krampslaag/Bikera/Componenten.docx

PCB componenten

# 1 Overzicht

- MCU: STM32, energiezuinig
- Lora transceiver
- EEC chip: elliptische curve berekening
- GPS/GNSS module
- E-ink display
- Accelerometer
- SD-kaart
- BMS voor 2-4 18650 batterijen
- Aansturing voor motor of solenoide

# 2 MCU: STM32

- Energiezuinig
- Net genoeg rekenkracht
- Geen zware crypto (externe EEC chip)

## 2.1 Flash schatting

Component | Flash
Boot + main app | ~10–20 kB
LoRaWAN stack | 20–40 kB
Drivers (SPI, I²C, UART) | 5–10 kB
QR-code lib | 5–10 kB
Display driver | 5–15 kB
Debug / utils | 5–10 kB

Minimim flash:

64 kB = krap
128 kB = comfortabel
256 kB = luxe

## 2.2 RAM schatting

Component | RAM
Stack + heap | ~4 kB
LoRa buffers | 2–4 kB
QR matrix | 1–2 kB
Display buffer (partial) | 1–4 kB
Sensor buffers | <1 kB

Minimum RAM:

16 kB = minimum
32 kB = veilig
64 kB = chill debuggen

## 2.3 Peripherals

Het is nog niet duidelijk welke modules met SPI, I²C of UART werken

Peripheral | | Aantal pinnen
SPI | - Lora transceiver - e-ink - SD-kaart | 3 (clk, miso, mosi) + 3 (cs)
I²C | - accelerometer | 2
UART | - GPS/GNSS - Bluetooth - debug logs | 2 2 2
ADC 10-12 bit | - Batterij spanning | 1
Timers (Intern) | - RTC wakeups - debouncing knoppen - watchdog
GPIO | Interrupts: - knoppen - Lora DIO - accelerometer - Motor/solenoid - Status LED | 2-4 1-3 ? 1 1-2 1
SWD | Serial wire debug | 2
NRST pin | Reset pin | 1
| | +2 (VCC en GND) = 24-31 totaal

## 2.4 Vereisten

- Cortex-M0+ of hoger
- ≥ 128 kB Flash
- ≥ 32 kB RAM
- 3× SPI (met DMA)
- 2× UART
- I²C
- ADC
- RTC
- Ultra-low power sleep modes
- SWD debug

Aantal SPI, UART en I²C is een gok, de meeste chips hebben wel genoeg van elk

## 2.5 Opties

https://www.rutronik.com/fileadmin/Rutronik/Supplier/STMicroelectronics/Landing_Pages/STM32L496xx_Family/RS4386_brstm32ulp.pdf

STM32L0 (https://www.st.com/en/microcontrollers-microprocessors/stm32l0-series.html) Cortex-M0+ Goedkoopste, meest zuinig, misschien net niet genoeg flash en RAM

STM32L1 (https://www.st.com/en/microcontrollers-microprocessors/stm32l1-series.html) Cortex-M3+ Iets krachtiger, iets minder zuinig

STM32L4 (https://www.st.com/en/microcontrollers-microprocessors/stm32l4-series.html) Cortex-M4 Nog krachtiger, ongeveer even zuinig als L0, duurder

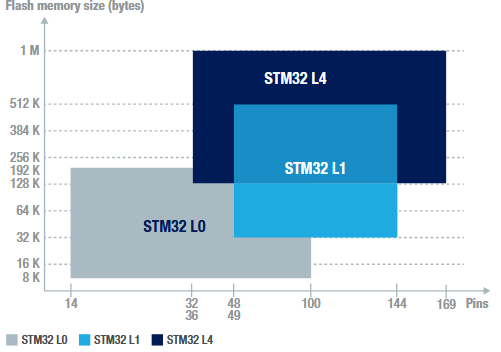
[picture p2: figure]
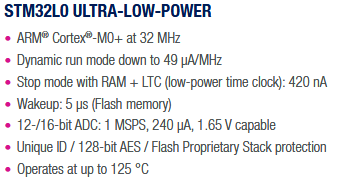
[picture p3: figure]
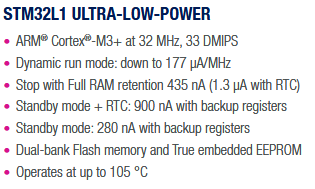
[picture p4: figure]
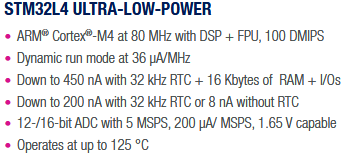
[picture p5: figure]
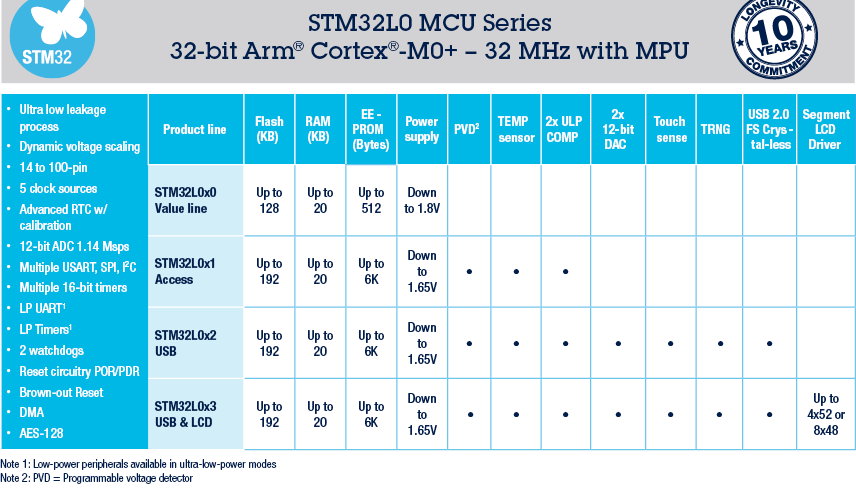
[picture p6: figure]
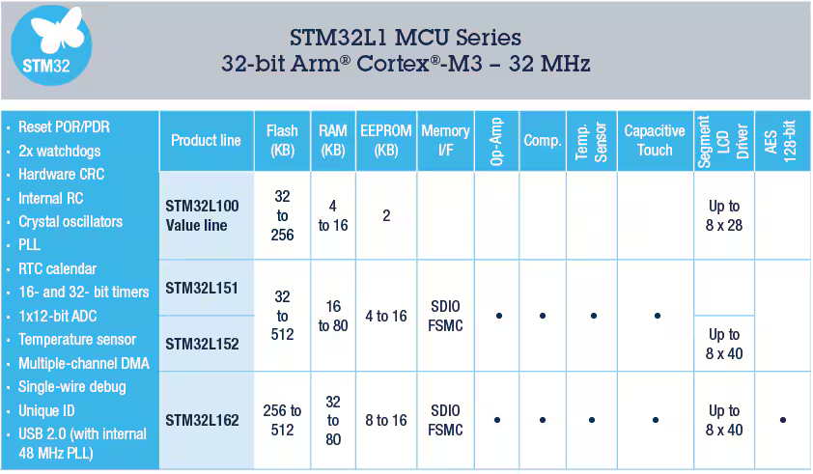
[picture p7: figure]
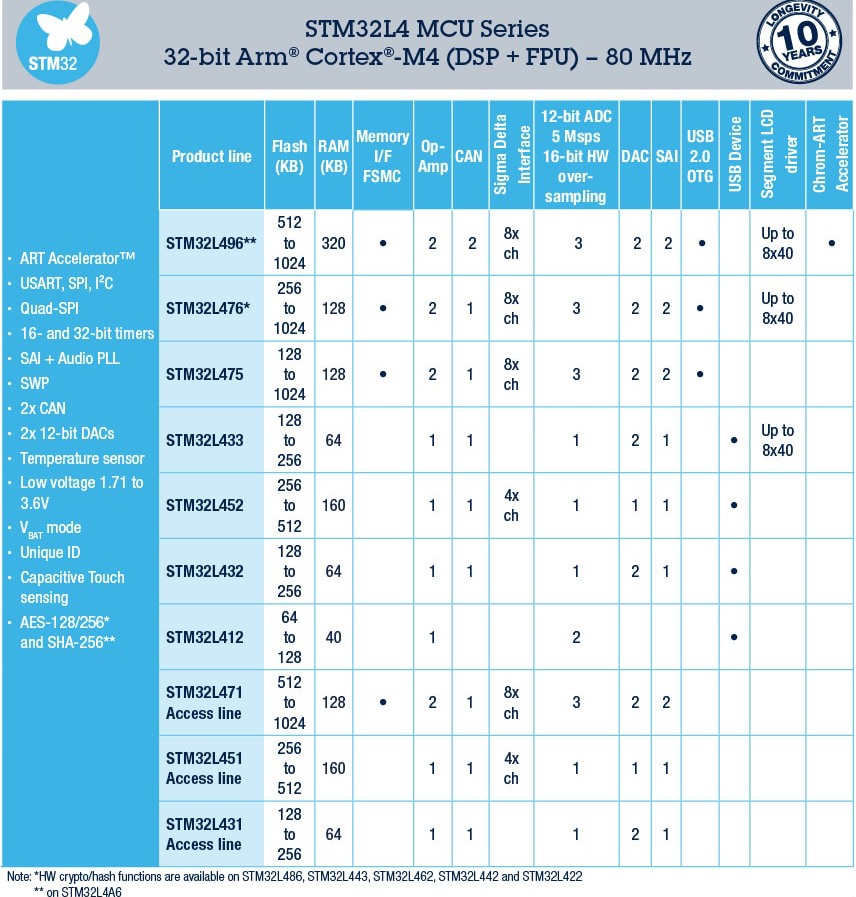
[picture p8: figure]
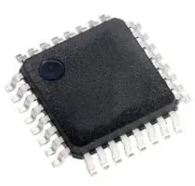
[picture p9: figure]

## 2.6 Vormfactor

24-31 pinnen nodig

Bij voorkeur LQFP32 of LQFP48

## 2.7 Voorbeeld van prijzen

https://www.digikey.be/en/products/filter/embedded-microcontrollers/685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

https://be.farnell.com/w/c/semiconductors-ics/microcontrollers/arm-microcontrollers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

## 2.8 Voorstel

Flash RAM pinnen

STM32L431CCT6TR (https://be.farnell.com/stmicroelectronics/stm32l431cct6tr/mcu-32bit-80mhz-lqfp-48/dp/3365485RL) Cortex-M4 256KB 64KB 48

STM32L071CZT6TR (https://be.farnell.com/stmicroelectronics/stm32l071czt6tr/mcu-32bit-32mhz-lqfp-48/dp/3365483RL) Cortex-M0+ 192KB 20KB 48

STM32L412CBT6P (https://be.farnell.com/stmicroelectronics/stm32l412cbt6p/mcu-32bit-80mhz-lqfp-48/dp/3933166) Cortex-M4 128KB 40KB 48

STM32L412KBT6 (https://be.farnell.com/stmicroelectronics/stm32l412kbt6/mcu-32bit-80mhz-lqfp-32/dp/2980922) Cortex-M4 128KB 40KB 32

STM32L422KBT6 (https://be.farnell.com/stmicroelectronics/stm32l422kbt6/mcu-32bit-80mhz-lqfp-32/dp/2980927) Cortex-M4 128KB 40KB 32

Zie vergelijking volgende pagina (Farnell)

Digikey lijkt goedkoper bij grote hoeveelheden (rangschik per prijs en kies price by quantity)

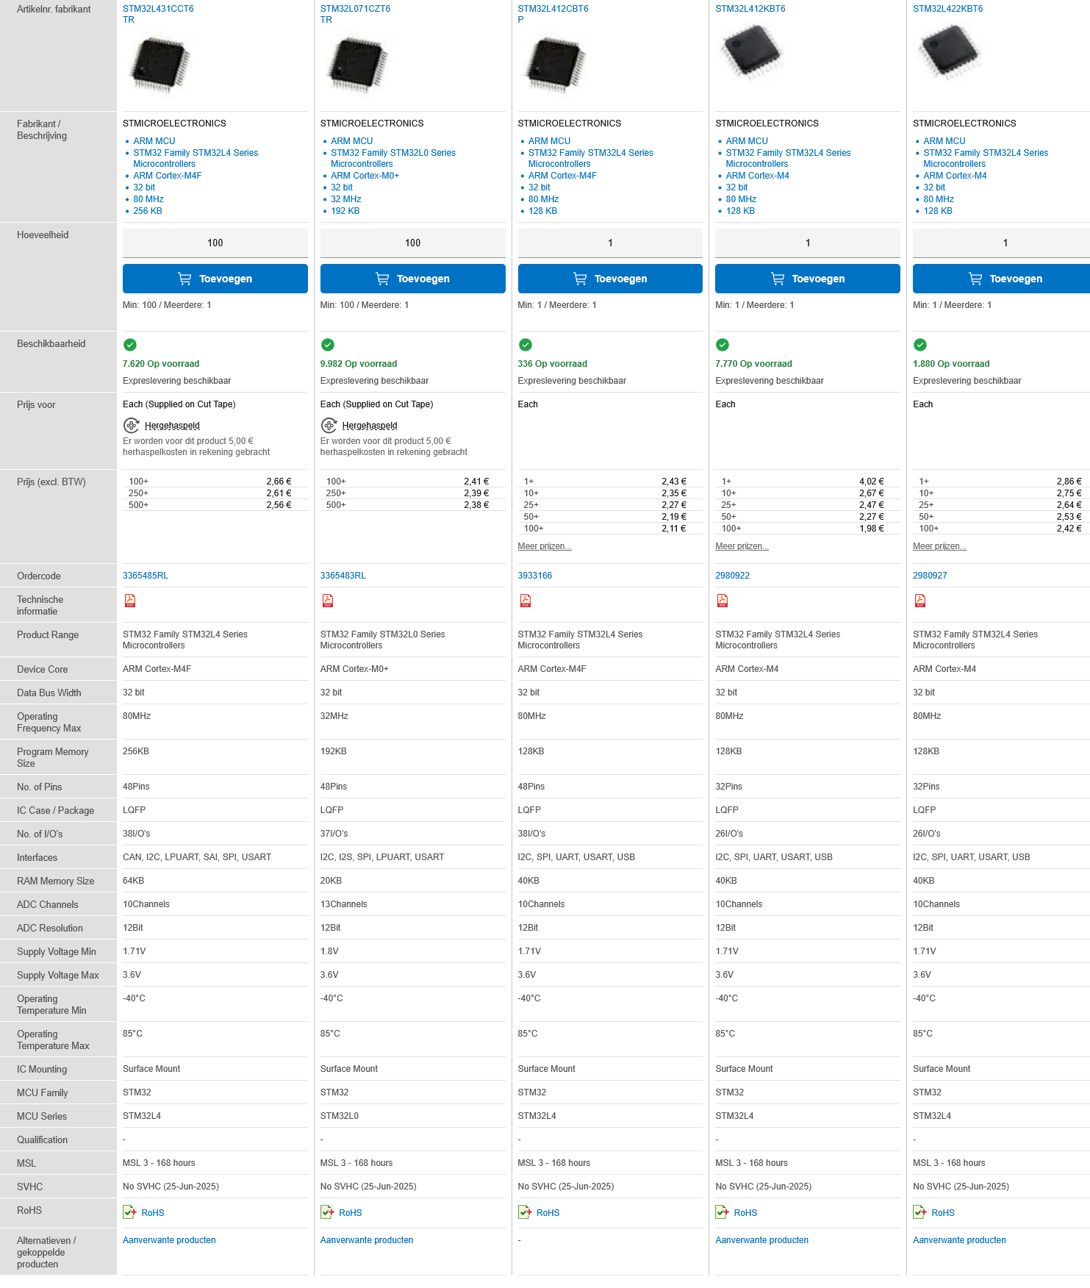
[picture p10: figure]

## 2.9 Keuze

Voor prototype:

STM32L431CCT6TR (https://be.farnell.com/stmicroelectronics/stm32l431cct6tr/mcu-32bit-80mhz-lqfp-48/dp/3365485RL) Cortex-M4 256KB flash 64KB ram LQFP-48

# 3 LoRa

- 868MHz voor Europa (863–870 MHz / EU868 / ISM band)
- LoRaWAN
- CE-gecertificeerd
- ETSI EN 300 220-conform
- RX-stroom ≈ 4–6 mA ?
- TX-stroom ≈ 40–120 mA (afhankelijk van het vermogen) ?
- Slaapstroom < 2 µA (idealiter < 1 µA)?
- SPI: betere timing, efficienter dan UART

Opties:

- Transceiver IC
  - bv. SX1261, SX1262, LLCC68 (SX127x is verouderd en minder efficient)
  - RF matching en antenne design zelf doen
- LoRa module
  - RF is al gedaan, gecertificeerd, alleen SPI + antenne
- STM32WL SoCs = STM32 + LoRa
  - Efficienter, goedkoper, moeilijker mee te werken

## 3.1 STM32 + LoRa?

STM32WL serie bevat LoRa radio

https://www.st.com/en/microcontrollers-microprocessors/stm32wl5x-ex.html

- Efficienter (geen SPI/UART, geen externe radio wakeups)
- I-CUBE-LRWAN en LoRaWAN stacks aangeboden door ST
- Goedkoper dan lora apart
- RF ontwerp moeilijker (antenne interface, ground keep-outs)
- Moeilijkere configuratie (EU regels, RF matching zelf instellen,…)
- Moeilijkere vormfactor (UQFPN, UFBGA)

## 3.2 Modules

Ebyte E22 series (https://www.cdebyte.com/Module-LoRa-SX1262)

- Bv. E22-900M30S, E22-900M22S, E22P-868M30S
- Gebaseerd op SX1262
- SPI
- Chinees, niet op digikey, farnell, mouser

WisDuo RAK3172 (https://docs.rakwireless.com/product-categories/wisduo/rak3172-module/overview/)

- met STM32WLE5CCU6
- UART interface
- SPI mogelijk?? “SPI voor communicatie met RF subsysteem van STM32WLE5CCU6”
- https://www.digikey.be/nl/products/detail/rakwireless-technology-limited/RAK3172-8-SM-NI/17138049

WisDuo RAK11720 (https://store.rakwireless.com/products/rak11720-ambiq-apollo3-module-for-lorawan?variant=43549376250054)

- LoRa + BLE 5
- https://www.digikey.be/nl/products/filter/rf-misc-ic-s-en-modules/863?s=N4IgTCBcDaIEoEEDSBGFB2MAGEBdAvkA

Murata CMWX1ZZABZ

- Zeer compact, duurder

Eventueel met GPS/GNSS:

LoRa Edge (https://wyldnetworks.com/blog/semtech-lora-edge-for-asset-tracking)

https://www.mouser.be/ProductDetail/Semtech/LR1110IMLTRT?qs=GedFDFLaBXFCcMA0cJwOqg%3D%3D

## 3.3 Keuze

Voor prototype:

WisDuo RAK11720 (https://store.rakwireless.com/products/rak11720-ambiq-apollo3-module-for-lorawan?variant=43549376250054)

Met MHF4 connector: https://www.digikey.be/nl/products/detail/rakwireless-technology-limited/RAK11720-8-SM-I/26861631

RF pinout: https://www.digikey.be/nl/products/detail/rakwireless-technology-limited/RAK11720-8-SM-NI/26861635

## 3.4 Antenne

WisDuo RAK11720 (https://store.rakwireless.com/products/rak11720-ambiq-apollo3-module-for-lorawan?variant=43549376250054) heeft 2 connectors, voor LoRa en BLE

### 3.4.1 RAK11720 LoRa vereisten

- 868MHz
- MHF4 connector
- 50Ω impedantie
- VSWR <= 2 of return loss < -10dB (beter VSWR <= 1.5 of return loss < -15dB)
- Gain 0–3 dBi (hoger wordt directioneel, verder bereik op vlak terrein maar minder geschikt voor steden)
- Lengte: ½ of ¼ golflengte (868MHz) is geschikt: ~8.6cm tot 17.3cm

### 3.4.2 Soorten antennes

- Antenne op PCB :
  - Goedkoper in productie
  - Moeilijker, gevoelig voor layout en enclosure, RF ervaring nodig
- FPC antenne: Met een draad naar flex PCB om te plakken
  - Eenvoudig, vrij compact
  - Gemakkelijkere certificatie
- Coil antenne: niet geschikt voor vibratie en schokken
- Externe antenne: niet geschikt voor fietsslot

FPC antenne voor prototype, eventueel PCB antenne later?

### 3.4.3 Opties

Op digikey zijn er 2 met MHF4 aansluiting en 868MHz.

3dB versterking, VSWR 2.5, €1 voor 1

https://www.digikey.be/nl/products/filter/rf-antennes/875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

Beste resultaat op farnell:

2.2dBi, VSWR 1.5, €2.69 voor 1

https://be.farnell.com/te-connectivity/l000551-05/rf-antenna-863-to-870mhz-2-2dbi/dp/4457734

### 3.4.4 Keuze

Voor prototype: farnell

Later losse draad? Zal moeten getest worden.

### 3.4.5 Losse draad

½ of ¼ golflengte: 8.6 cm of 17.2 cm

Impedantie moet ~50 Ω zijn voor RAK11720

Moeilijk te testen op MHF4-connector voor prototype, eventueel RF pinout gebruiken later?

Monopool

1 draad gebogen rond binnenkant van behuizing

Goede groundplane nodig

Beter met RF pinout (niet MHF4)

Ideale impedantie en VSWR bij resonantie (perfecte geometrie, rechte antenne):

8.6 cm: ~ 73 Ω , VSWR ≈ 1.5

17.2 cm: ~36-39 Ω, VSWR ≈ 1.3 – 1.6

8.6cm monopool in fietsslot:

  - Resonantiefrequentie kan zakken (en VSWR stijgen)
  - Impedantie kan 20-60Ω zijn met wat reactantie
  - VSWR kan 1.2-3 zijn afhankelijk van de layout

17.2 cm monopool in fietsslot:

  - Veel reactantie, hoge VSWR
  - Wordt niet veel gebruikt

Dipool

- 2x 8.6 cm
- Gebogen, of licht gebogen in V-vorm of evt. recht in V-vorm
- In vrije ruimte, recht:
  - Impedantie ≈ 73 Ω bij resonantie
  - VSWR op 50 Ω ≈ 1.5:1
- Gebogen in fietsslot:
  - Resonantie zal zakken
  - Impedantie kan dichter bij 50 Ω zakken
  - Draad inkorten kan resonantie terug naar 868MHz brengen
  - Positie (horizontaal, verticaal) bepaalt uitstraling

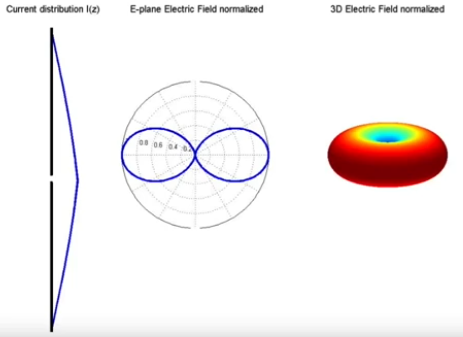
[picture p11: figure]

Suggestie: dipool in V-vorm, recht of licht gebogen. Beginnen met 2x9cm en trimmen tot resonantie 868MHz is, impedantie ongeveer 50 Ω en VSWR laag genoeg. Of tot prestatie goed is.

### 3.4.6 BLE

Aparte antenne nodig voor BLE (WisDuo RAK11720 (https://store.rakwireless.com/products/rak11720-ambiq-apollo3-module-for-lorawan?variant=43549376250054) heeft 2 connectors)

Vereisten:

- 2.4-2.5GHz, 50Ω MHF4 bluetooth antenne.
- Gain: 0-3dBi (=omnidirectioneel) & goede uitstralingsefficientie (>=40-50%)
- VSWR < 2:1 (≈ −10 dB return loss)
- Lange kabels kunnen ruis opnemen, kort is beter
- Best omnidirectioneel, orientatie maakt niet veel uit.

Soorten antennes: zoals LoRa. FPC antenne lijkt best.

Opties:

- Digikey (https://www.digikey.be/nl/products/filter/rf-antennes/875):

AANI-FB-0086-0100W lijkt best, is beschikbaar in 3 lengtes: 100mm (https://www.digikey.be/nl/products/detail/abracon-llc/AANI-FB-0086-0100W/25558929), 150mm (https://www.digikey.be/nl/products/detail/abracon-llc/AANI-FB-0086-0150W/25558928), 200mm (https://www.digikey.be/nl/products/detail/abracon-llc/AANI-FB-0086-0200W/25558936)

€2.14 - €2.21

- De site van de RAK module raadt deze aan ($3): https://store.rakwireless.com/products/2-4ghz-wifi-ble-pcb-antenna-mhf-4
- Bij Farnell zijn er geen FPC-antennes van 2.4GHz
- Bij Mouser zijn er maar 2 geschikte (https://www.mouser.be/c/passive-components/antennas/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) bluetooth antennes met MFH4 aansluiting, van €4.35 en €4.84

Keuze:

AANI-FB-0086-0100W (100mm) (https://www.digikey.be/nl/products/detail/abracon-llc/AANI-FB-0086-0100W/25558929) - €2.21 voor 1

# 4 ECC secure element

## 4.1 Vereisten

- Low power (slaapstroom < 1µA)
- I²C
- NVM key storage, root of trust ·
- Niet NIST P-256
  - Solana: Ed25519
  - Of Ethereum: Keccak-256
- SHA-256 (hash) voor transacties
- DIP vormfactor of DIP breakout voor socket (bv. SOIC-to-DIP)

## 4.2 Opties:

### 4.2.1 Microchip CryptoAuthentication serie

Microchip ATECC108A (https://ww1.microchip.com/downloads/aemDocuments/documents/OTH/ProductDocuments/DataSheets/Atmel-8895S-CryptoAuth-ATECC108A-Datasheet-Summary.pdf): voor key storage en ECDSA (Elliptic Curve Digital Signature Algorithm)

Microchip ATECC508A (https://ww1.microchip.com/downloads/en/DeviceDoc/20005928A.pdf): heeft ook ECDH (Elliptic Curve Diffie-Hellman) en secure boot

Microchip ATECC608A (https://www.mouser.com/datasheet/2/268/ATECC608A_CryptoAuthentication_Device_Summary_Data-3441583.pdf) / ATECC608B (https://ww1.microchip.com/downloads/aemDocuments/documents/SCBU/ProductDocuments/DataSheets/ATECC608B-CryptoAuthentication-Device-Summary-Data-Sheet-DS4000223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): meer geavanceerd (TLS 1.3, AES, betere security)

- TECC608B is hetzelfde als ATECC608A, met een paar kleine verbeteringen. ATECC608A heeft I²C problemen. https://ww1.microchip.com/downloads/en/Appnotes/Migrating-from-the-ATECC608A-to-the-ATECC608B-DS40002237A.pdf
- Slaapstroom <150 nA, actief 2–3 mA
- NIST P‑256
- ECDSA/ECDH met secure key storage
- AES-128: Encrypt/Decrypt
- I²C en single wire
- 8-pin SOIC en UDFN

### 4.2.2 ATECC608B device ordering codes

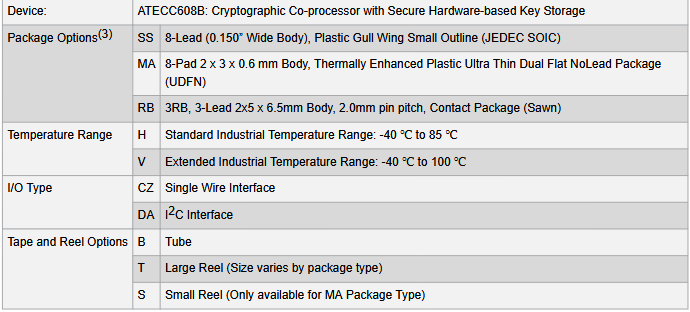
[picture p12: figure]

### 4.2.3 NXP EdgeLock SE050 (https://www.mouser.be/new/nxp-semiconductors/nxp-edgelock-se050/)

- Higher-end, meer features (CC EAL 6+ / FIPS-class security, TLS offload, meer algoritmes)
- Duurder
- HX2QFN20 vormfactor, voor reflow solderen

## 4.3 Keuze

Prototype: ATECC608B-SSHDA-T

8-pin SOIC, I²C, tape & reel

Digikey (https://www.digikey.be/nl/products/detail/microchip-technology/ATECC608B-SSHDA-T/13415162): €0.76 (€0.7488 voor 25 en €0.68541 voor 4000)

Mouser (https://www.mouser.be/ProductDetail/Microchip-Technology/ATECC608B-SSHDA-T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): €0.77 (0.649 voor >25)

Farnell (https://be.farnell.com/microchip/atecc608a-sshda-t/cryptoauthentication-40-to-85deg/dp/2920872):

Eventueel NXP EdgeLock SE050 (https://www.mouser.be/new/nxp-semiconductors/nxp-edgelock-se050/)

## 4.4 SOIC-to-DIP adapter

De ECC-chip wordt op een IC-voet geplaatst. De ATECC608B-SSHDA-T is een SMD component (SOIC-8) en heeft een SOIC-8-to-DIP adapter nodig.

- FIT0290 (https://www.digikey.nl/en/products/detail/dfrobot/FIT0290/6588424)
  - €0.47 digikey, inclusief pin headers

## 4.5 IC-voet

- 1-2199298-2 (https://www.te.com/commerce/DocumentDelivery/DDEController?Action=srchrtrv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)
  - €0.206 mouser (https://www.mouser.be/ProductDetail/TE-Connectivity/1-2199298-2?qs=fK8dlpkaUMtEKa4wabwOXQ%3D%3D)

# 5 GPS/GNSS

GPS zal alleen gebruikt worden als de fiets gestolen is. Locatiebepaling en snelheid/afstand meten gebeurt met de accelerometer en LoRa.

## 5.1 Vereisten

- Multi‑GNSS (GPS + Galileo + BeiDou + GLONASS) is meer precies en betrouwbaar, maar ook duurder
- Low power (sub‑mW standby)
- Meter-level precisie is genoeg
- Update rate (communicatie met MCU) en fix rate (Locatiebepaling) mogen laag zijn -> 1Hz, of zelfs kleiner?
- Interface: UART of I2C
- Geschikt voor buiten

## 5.2 Opties

U-blox en Quectel hebben goede modules

### 5.2.1 U-blox

MAX-M10 series (https://www.u-blox.com/en/product/max-m10-series)

- Ultra low power (<25mW)
- GPS, GLONASS, Galileo, BeiDou
- Goede performance met kleine antennes
- MAX-M10M-20B is nieuw en heeft ook:
  - SBAS (Satellite-Based Augmentation System)
  - LNA (low noise amplifier)
  - SAW filter (Surface Acoustic Wave)
- Goedkoopste modules op mouser (https://www.mouser.be/c/embedded-solutions/wireless-rf-modules/gnss-gps-modules/?q=u-blox&sort=pricing)

MAX-M10M-20B (https://www.mouser.be/datasheet/3/3699/1/MAX_M10M_20B_DataSheet_UBXDOC_963802114_13063.pdf) lijkt de beste optie van U-blox

- Mouser (https://www.mouser.be/ProductDetail/u-blox/MAX-M10M-20B?qs=bpu3f%2FCR1jxLHPI3qGoNEA%3D%3D): €5.53, Nieuw: beschikbaar vanaf 09/04/26
- Digikey (https://www.digikey.be/nl/products/detail/u-blox/MAX-M10M-20B/28314774?s=N4IgTCBcDaILIEEAaBaOBGADHFZMCEQBdAXyA): €5.84 (€5.2 per 1000)
- Niet bij Farnell
- Verbruik, ter vergelijking met Quectel:

### 5.2.2 Quectel

Zie brochure (https://www.quectel.com/content/uploads/2026/01/Quectel_Product_Brochure_V8.5_2026.pdf) p.91-93 (88-90 op blad) voor vergelijking

Goedkoopste modules op Digikey (https://www.digikey.be/nl/products/filter/rf-zendontvangermodules-en-modems/872)

Goedkoopste modules op Mouser

(https://www.mouser.be/c/rf-wireless/wireless-modules/gnss-gps-modules/?m=Quectel&sort=pricing)

LC76G serie

- (https://www.quectel.com/content/uploads/2024/03/Quectel_LC76G_Series_GNSS_Specification_V1.1-1-1.pdf)Goedkoop
- GPS, GLONASS, BDS, Galileo and QZSS
- AGNSS: snellere opstart (first time to fix) -> niet relevant (sattelietdata moet gedownload worden)
- Integrated LNA
- LC76G (PA) heeft laagste verbruik (10mA operatie, 5.5mA ALP mode, 13µA backup mode)
- Mouser prijzen: LC76GABMD (https://www.mouser.be/ProductDetail/Quectel/LC76GABMD?qs=vvQtp7zwQdPmNdoEwjtHVg%3D%3D) LC76GPAMD (https://www.mouser.be/ProductDetail/Quectel/LC76GPAMD?qs=vvQtp7zwQdMfDuCTmjRUww%3D%3D) LC76GPBMD (https://www.mouser.be/ProductDetail/Quectel/LC76GPBMD?qs=17ckDYBRdelT6eALYgwPNA%3D%3D)

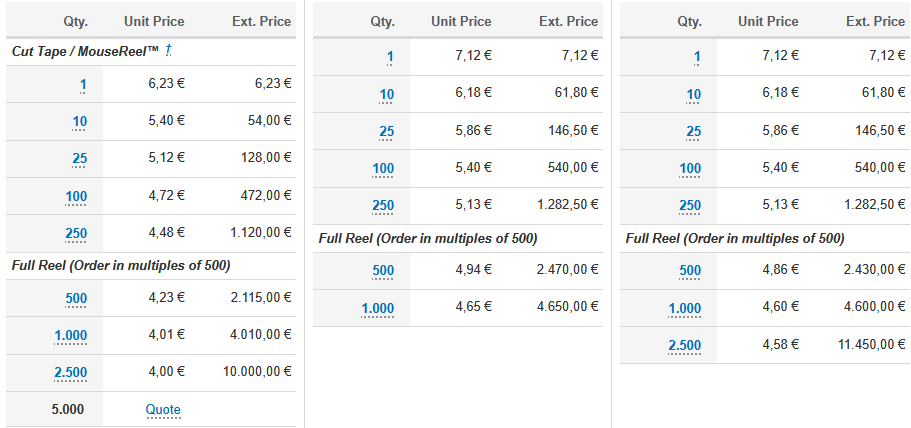
[picture p13: figure]

- Digikey prijzen:

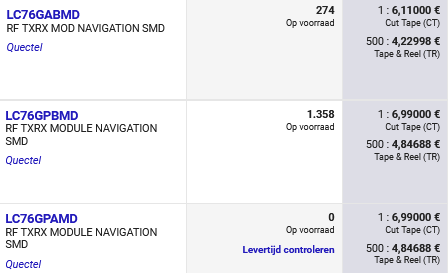
[picture p14: figure]

Quectel LC760Z (https://www.quectel.com/content/uploads/2025/03/Quectel_LC760Z_GNSS_Specification_V1.3.pdf)

- Goedkoopste Mouser (https://www.mouser.be/ProductDetail/Quectel/LC760Z00AAMD) Digikey (https://www.digikey.be/nl/products/detail/quectel/LC760Z00AAMD/22214009?s=N4IgTCBcDaIDIGEDsA2ADALRAXQL5A) (niet in voorraad)

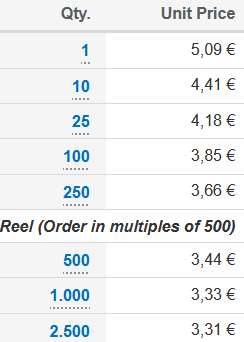
[picture p15: figure]
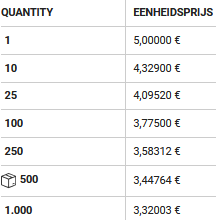
[picture p16: figure]

- GPS, GLONASS, Galileo, BDS (B1I & B1C) and QZSS
- Iets meer verbruik in operatie, standby mode van 1.4mA

Ter vergelijking: verbruik van U-blox MAX-M10M-20B (https://www.mouser.be/datasheet/3/3699/1/MAX_M10M_20B_DataSheet_UBXDOC_963802114_13063.pdf):

## 5.3 Voorstel:

U-blox MAX-M10M-20B (https://www.mouser.be/datasheet/3/3699/1/MAX_M10M_20B_DataSheet_UBXDOC_963802114_13063.pdf)

Of Quectel LC76GPAMD (https://www.mouser.be/ProductDetail/Quectel/LC76GPAMD?qs=vvQtp7zwQdMfDuCTmjRUww%3D%3D)

Quectel LC76GPAMD (https://www.mouser.be/ProductDetail/Quectel/LC76GPAMD?qs=vvQtp7zwQdMfDuCTmjRUww%3D%3D) heeft minder stroomverbruik en is goedkoper bij grote volumes.

U-blox MAX-M10M-20B (https://www.mouser.be/datasheet/3/3699/1/MAX_M10M_20B_DataSheet_UBXDOC_963802114_13063.pdf) heeft beter ecosysteem (u-center, AssistNow, veel voorbeeldontwerpen) en is beter voor kleine/slechte antennes, (SAW+LNA & Super-S technologie). Stroomverbruik is ook al klein.

## 5.4 Keuze

Quectel LC76GPAMD (https://www.mouser.be/ProductDetail/Quectel/LC76GPAMD?qs=vvQtp7zwQdMfDuCTmjRUww%3D%3D)

# 6 GPS antenne

Er zijn actieve en passieve GPS antennes. Actieve antennes zijn nauwkeuriger, hebben een geïntegreerde LNA (low noise amplifier) en hebben voeding nodig. Ze zijn beter geschikt om verder van de ontvanger te plaatsen. Passieve antennes zijn eenvoudiger, goedkoper, zuiniger en nauwkeurig genoeg voor deze toepassing. De Quectel LC76GPAMD (https://www.mouser.be/ProductDetail/Quectel/LC76GPAMD?qs=vvQtp7zwQdMfDuCTmjRUww%3D%3D) heeft ook een ingebouwde LNA.

## 6.1 Opties

## 6.2 Soorten antennes

- Helical antenna
- patch antenne

## 6.3 Vereisten

- 1-10m nauwkeurigheid is genoeg
- De datasheet (https://www.sigmaelectronica.net/wp-content/uploads/2024/07/quectel_lc76g_series_hardware_design_v1-2.pdf) (p. 38) toont deze specificaties voor een passieve antenne:

Frequency Range: 1559–1606 MHz

Polarization: RHCP (right-hand circular polarization)

VSWR: < 2 (Typ.)

Passive Antenna Gain: > 0 dBi

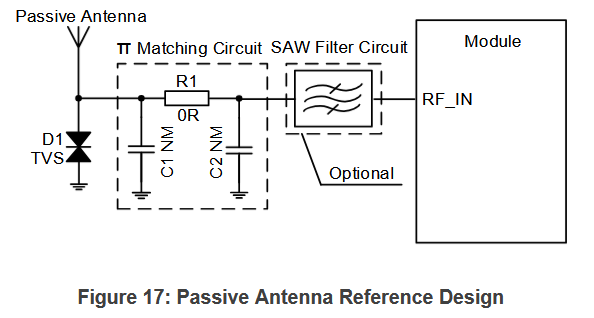
[picture p17: figure]

C1, R1, and C2 are reserved for matching antenna impedance. By default, R1 is 0 Ω, and C1 and C2 are

not mounted. They should be placed near the antenna in the actual layout. D1 is an electrostatic

discharge (ESD) protection device to protect the RF signal input from the potential damage caused by

ESD. The junction capacitance of D1 cannot be more than 0.6 pF and a transient voltage suppressor is

recommended. RF trace impedance should be controlled to 50 Ω and trace length should be kept as

short as possible.

## 6.4 Keuze

Voor prototype: YFGA003AA (https://www.digikey.be/nl/products/detail/quectel/YFGA003AA/21273116) FPC antenne

- €1.31
- 100mm kabel
- Er is een aparte connector nodig, de Quectel LC76GPAMD (https://www.mouser.be/ProductDetail/Quectel/LC76GPAMD?qs=vvQtp7zwQdMfDuCTmjRUww%3D%3D) GPS heeft geen connector.
- Eventueel kunnen we de kabel proberen doorknippen en rechtstreeks solderen

Later kunnen we een patch antenne proberen, of een draadantenne zoals bij LoRa.

# 7 E-ink display

## 7.1 Vereisten

- Zwart-wit, hoog contrast
- Grootte en resolutie
  - Klein, vierkant
  - 1.54 inch
  - Voldoende pixels voor QR
  - 1.54″ 200×200 wordt veel gebruikt voor QR codes
- QR code versie? (zie https://www.qrcode.com/en/about/version.html)
  - 21x21 is kleinst
  - Berekening grootst mogelijke QR code: De kleinste scanbare QR code is 1x1cm 38x38 pixel -> 0.263mm per pixel 1.54” = 27.12x27.12mm -> 200x200 pixels = 0.135mm per pixel kleinste mogelijke QR pixel is 2x2 pixels op het scherm (0.27x0.27mm) dus grootste QR code is 97x97 (versie 20)
- I²C of SPI?
  - I2C is efficienter op lage snelheden
  - De meeste E-inks zijn SPI
  - Scherm wordt niet veel ge-update, SPI is ok
- geen partial refresh of fast update nodig

## 7.2 Paneel of module?

### 7.2.1 Paneel

- SPI via korte flat-flex (FPC) kabel ( 0.5mm pitch, 22 of 24Pin)
  - Kan verlengd worden
- Fragiel
- Goedkoper
- Analoge front-end zelf ontwerpen (voedingscircuit: VGH, VGL, AVDD/VSH, VCOM,…)
  - Circuit hangt af van paneel, moet veranderd worden als paneel wordt veranderd
- Monteren op aparte PCB
- Specifieke driver per paneel

### 7.2.2 Module

- Veel eenvoudiger voor prototype
- Later kan schema van datasheet gekopieerd worden naar PCB en paneel gebruikt worden.

### 7.2.3 Andere opties

- Paneel + adapter board (https://eckstein-shop.de/GooDisplay-24Pin-Serial-ePaper-Screen-HAT-Adapter-Board-DESPI-C02-EN): met voedingscircuit
- Een driver board met ESP32 of ESP8266 bestaat ook, maar is meer bedoeld voor wifi

### 7.2.4 Opties

Panelen:

- Orient Display 1.54” 200x200 paneel (https://www.digikey.be/nl/products/detail/orient-display/AES200200A00-1-54ENRS/15198467)
  - Enige bij digikey
  - $7.2, niet beschikbaar in €
- Geen 1.54” E-inks bij Mouser of Farnell
- Good Display (https://www.good-display.com/product/51/) 1.54” 200x200 paneel: €5.3 (https://www.good-display.com/product/388.html)
  - GoodDisplay heeft ook paneel dat met lagere temparetuur werkt (-25-50°C ipv. 0-50°C), maar die is niet geschikt voor in de zon.
- Waveshare 1.54” 200x200 paneel: €5.16 (https://www.waveshare.com/1.54inch-e-paper.htm?amazon)
  - Datasheet (https://files.waveshare.com/upload/e/e5/1.54inch_e-paper_V2_Datasheet.pdf)
- Elecrow: 1.54” 152x152 paneel (https://www.elecrow.com/1-54-inch-152-152-e-paper-display-black-white-e-ink-display-with-spi-communication.html): €2.91
  - SSD1680

Modules:

- Waveshare 1.54” module: €8.61 (https://www.waveshare.com/1.54inch-e-Paper-Module.htm)
  - Aansluiting: 8-pin JST PH 2.0mm SMT Header Horizontal Right Angle Side (SPI interface)

## 7.3 Keuze

- Waveshare 1.54” module: €8.61 (https://www.waveshare.com/1.54inch-e-Paper-Module.htm)

# 8 Accelerometer

Afstand meten is niet mogelijk door error accumulatie (Can an IMU Alone Perform Odometry? (https://guidenav.com/blog/can-an-imu-alone-perform-odometry/)).

Accelerometer kan gebruikt worden voor interrupts (wake up bij beweging), om te detecteren of de fiets gestolen wordt en evt. om LoRa en GPS update rate te bepalen.

## 8.1 Vereisten

- Low power (<5µA)
- Output data rate (ODR): 10-50Hz is genoeg (lager = zuiniger)
- Programmable threshold motion / free-fall interrupts
- Sleep-to-wake and return-to-sleep gebaseerd op beweging
- FIFO? Data opslaan als MCU slaapt
- Kracht: tot 2g geparkeerd (sabotage detectie), tot 4g tijdens fietsen

## 8.2 Opties

Moeilijk met hand te solderen -> breakout voor prototype?

LIS2DH12 (https://www.st.com/content/ccc/resource/technical/document/datasheet/12/c0/5c/36/b9/58/46/f2/DM00091513.pdf/files/DM00091513.pdf/jcr:content/translations/en.D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)

- €1.37 digikey (https://www.digikey.be/nl/products/detail/stmicroelectronics/LIS2DH12TR/4899892)
- Eventueel breakout bord voor prototype: €6 bij tinytronics (https://www.tinytronics.nl/en/sensors/acceleration-rotation/dfrobot-gravity-i2c-triple-axis-accelerometer-lis2dh12)
- Ultra-low-power (tot ~2 µA)
- I²C/SPI,
- wake/sleep logic
- ±2/4/8/16 g
- 10-bit, 32-level FIFO buffer for each channel (X, Y, Z)

LIS2DW12 (https://dfimg.dfrobot.com/wiki/23156/SEN0405_lis2dw12_datasheet_1.0.pdf)

- Gelijkaardig aan LIS2DH12, met minder verbruik en minder ruis
- €1.19 digikey (https://www.digikey.be/nl/products/detail/stmicroelectronics/LIS2DW12TR/7348326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) (niet op voorraad)
- €1.19 mouser (https://www.mouser.be/ProductDetail/STMicroelectronics/LIS2DW12TR?qs=u4fy%2FsgLU9NZAt0DqrAehA%3D%3D) (ook niet op voorraad)
- €1.31 farnell (https://be.farnell.com/stmicroelectronics/lis2dw12tr/lga-12-i-mems-digital-o-p-motion/dp/2849615)
- €5.5 tinytronics (https://www.tinytronics.nl/en/sensors/acceleration-rotation/dfrobot-fermion-triple-axis-accelerometer-spi-i2c-lis2dw12) (breakout)
- 50 nA in power-down mode, below 1 μA in active low-power mode
- Very low noise: down to 1.3 mg RMS in low-power mode

LIS3DH = LIS2DH12 met 3 ADC inputs.

ADXL362 of ADXL363

- Zeer laag verbruik
- SPI
- Te duur (>€5)

BMA400 (https://www.digikey.be/nl/products/detail/bosch-sensortec/BMA400/8634935)

## 8.3 Keuze:

LIS2DW12 (https://dfimg.dfrobot.com/wiki/23156/SEN0405_lis2dw12_datasheet_1.0.pdf):

- €5.5 tinytronics (https://www.tinytronics.nl/en/sensors/acceleration-rotation/dfrobot-fermion-triple-axis-accelerometer-spi-i2c-lis2dw12) (breakout) voor prototype
- Bij digikey, mouser of Farnell voor finaal product.

# 9 SD-kaart

Alleen voor prototype

SD adapter module bij tinytronics (https://www.tinytronics.nl/en/data-storage/modules/sd-card-adapter-module-3.3v-5v)

- €2.5
- Module met 2x8 pin header
- SPI
- 3.3V

# 10 FRAM geheugen

FRAM (Ferroelectric Random Access Memory): zoals EEPROM, maar beter.

- Hoge snelheid, zoals RAM
- Niet volatile, zoals EEPROM
- Meer write cycles (10¹⁴)
- Zuiniger

Keuze: FM24V01A-GTR (https://www.infineon.com/assets/row/public/documents/10/49/infineon-fm24v01a-128-kbit-16k-x-8-serial-i2c-f-ram-datasheet-en.pdf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) (€2.99 Digikey (https://www.digikey.be/nl/products/detail/infineon-technologies/FM24V01A-GTR/5210532))

- 128-Kbit ferroelectric random access memory (F-RAM) logically organized as 16K × 8
- Fast two-wire serial interface (I2C)
- Low power consumption
  - 175-A active current at 100 kHz
  - 150-A standby current
  - 8-A sleep mode current
- 8-SOIC (https://www.centralsemi.com/pdfs/case/soic-8pd.pdf)

# 11 Battery management system

## 11.1 Batterijen

Twee tot vier 18650 Li-ion batterijen in parallel.

Het is aan te raden om batterijen van een bekend merk te gebruiken. Slechte productiekwaliteit kan gevaarlijk zijn: https://www.lumafield.com/battery-report#battery-quality-report

## 11.2 Load sharing

https://www.microtype.io/blog/lithium-ion-battery-charger-circuit-load-sharing

Als de batterij rechtstreeks als voeding wordt gebruikt wordt de stroom bij het laden gesplitst tussen batterij en systeem. De batterij wordt dan minder efficiënt opgeladen en het laad-IC zou bij een volle batterij niet uitschakelen.

Dat kan met wat extra componenten, in dit schema wordt het systeem (buck/regulator) tijdens laden gevoed met 5V.

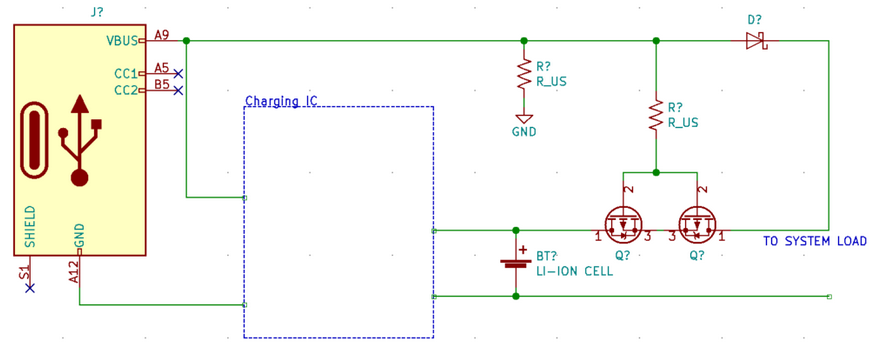
[picture p18: figure]

Er zijn ook IC’s met geïntegreerde load sharing (een aansluiting voor de batterij en uitgang Vsys).

## 11.3 Laadstroom

Laadstroom is afhankelijk van capaciteit en C-rating.

Bv. 1C -> 1A voor 1000mAh (opgeladen in ~1u) of 2A voor 2000mAh,…

0.5C -> 0.5A voor 1000mAh

De meeste 18650 batterijen zijn 0.5C-1C en 2600-3400mAh.

Afhankelijk van de batterij kunnen twee in parallel met 2.5A of meer worden opgeladen.

USB-poorten zonder power delivery (PD) leveren tussen 500mAh en 3A.

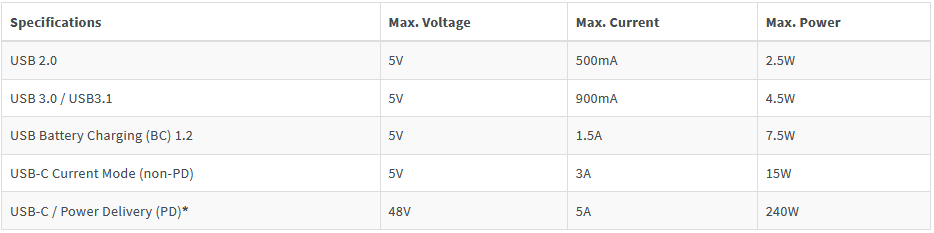
[picture p19: figure]

Er zijn 3 soorten USB poorten:

- Standard Downstream Port (SDP) - power is limited to the default power of the applicable USB specification (USB 2.0 or USB 3.x)
- Dedicated Charging Ports (DCP) - delivers power only (no data) up to 1.5A
- Charging Downstream Port (CDP) - capable of delivering both data and power up to 1.5A.

Er is een IC nodig dat de juiste stroom kan trekken afhankelijk van de USB poort. Bij USB 2.0 wordt Data Contact Detect (DCD) gebruikt om via de datalijnen te onderscheiden tussen een SDP-poort (100mA of 500mA) en DCP of CDP poort (1.5A) (USB Battery Charging Specification, Rev 1.2).

Bij USB-C worden de CC-pinnen gebruikt om de max. laadstroom te detecteren (zonder PD, tot 3A)

https://zbotic.in/usb-type-c-connector-power-delivery-and-data-wiring-guide/

Current advertisement (without PD): A USB-C charger advertises its current capability by placing a resistor on the CC pin:

  - 56k ohm pull-up: Default USB current (500mA USB 2.0, 900mA USB 3.0)
  - 22k ohm pull-up: 1.5A at 5V
  - 10k ohm pull-up: 3A at 5V

For device that draws 5V 1.5A without PD:

Place 5.1k ohm resistor from CC1 to GND

Place 5.1k ohm resistor from CC2 to GND

These resistors tell the charger:

"I am a USB-C device, provide appropriate current"

A PD charger will detect 5.1k (sink) and provide 5V

## 11.4 Opties - laders

TP4056: max. 1A, geen load sharing, niet geschikt

### 11.4.1 Power path IC’s met selecteerbare ingangstroom

Aparte IC nodig om USB-poort te selecteren, dan kan de max. ingangstroom bepaald worden. (bv. FSA832 (https://www.mouser.com/ds/2/149/FSA832-260289.pdf): USB 2.0 charger detection voor BC1.2, tot 1.5A, geen USB-C)

- MCP73871 (https://ww1.microchip.com/downloads/aemDocuments/documents/APID/ProductDocuments/DataSheets/MCP73871-Data-Sheet-DS20002090F.pdf)
  - ~€1.5-2
  - Load sharing
  - Tot 1A laadstroom, ingang tot 1.8A
  - Selecteerbare ingangstroom (USB 100mA, 500mA en 1.8A)
- bq2403x (https://www.ti.com/lit/ds/symlink/bq24032a.pdf)
  - ~€2-4
  - Tot 2A
  - 3.3-V Integrated LDO Output (30mA)
  - Selecteerbare ingangstroom (USB 100mA, 500mA en DC input)
- MAX8903 (https://www.analog.com/media/en/technical-documentation/data-sheets/MAX8903-MAX8903Y.pdf)
  - ~€4-7
  - Load sharing
  - Laadstroom tot 1.5A, ingang tot 2A
  - Selecteerbare ingangstroom (USB 100mA, 500mA en DC input)

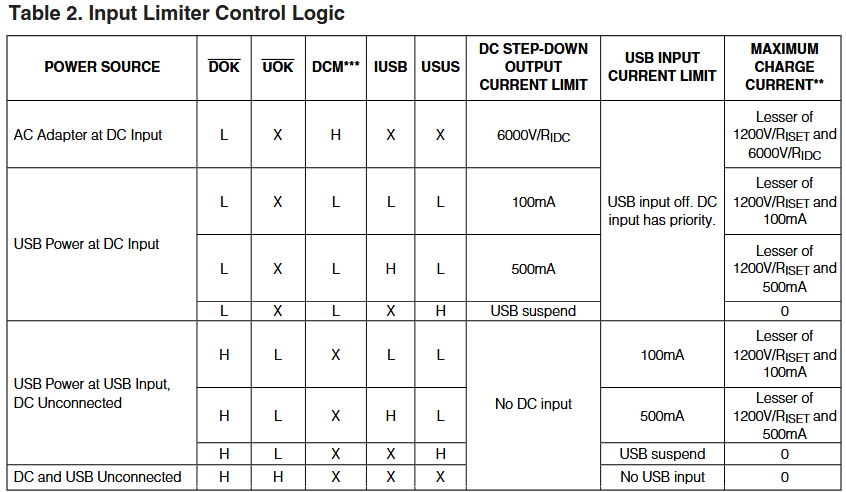
[picture p20: figure]

    - Als bv. de CHG_DET pin van de FSA832 (https://www.mouser.com/ds/2/149/FSA832-260289.pdf) lader-detectie-IC rechtstreeks met de DCM pin van MAX8903 verbonden wordt, zal de input gelimiteerd worden tot 500mA bij een standard downstream usb-poort (SDP) en hoger bij een DCP of CDP poort. 100mA kan waarschijnlijk genegeerd worden. Dan moet bij een USB-C verbinding de CC-pinnen apart bekeken worden.
- LTC4066 (https://www.analog.com/media/en/technical-documentation/data-sheets/4066fc.pdf)
  - ~€4-6
  - Seamless Transition Between Input Power Sources: Li-Ion Battery, USB and 5V Wall Adapter
    - 100mA / 500mA / oneindig
- STw4102 (https://www.st.com/content/ccc/resource/technical/document/datasheet/04/0c/9f/ee/ff/aa/48/a5/CD00149849.pdf/files/CD00149849.pdf/jcr:content/translations/en.C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)
  - Dual USB/wall adapter Li-ion battery charger with gas gauge
  - Laadstroom tot 1A
  - Support for currents higher than 1 A using external components
  - Battery voltage monitor with 7-12 bit AD converter
  - I²C interface for device monitoring and control
  - Charge status & power detection output

### 11.4.2 IC’s met USB-poort detectie

Kan je de USB data lijnen nog gebruiken voor STM32?

- MAX77751 (https://www.analog.com/media/en/technical-documentation/data-sheets/MAX77751.pdf)
  - ~€2-3.6
  - Integrated USB Detection
    - CC Detection for USB Type-C
    - BC1.2 Detection for Legacy SDP, DCP, and CDP
    - Automatic Input Current Limit Configuration
    - Input Voltage Regulation with Adaptive Input
    - Current Limit (AICL)
  - 3.15A Maximum Charging Current

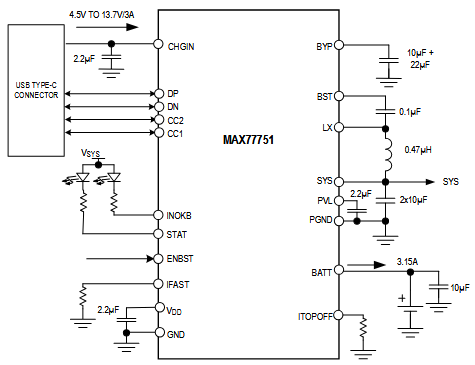
[picture p21: figure]

- BQ25895 (https://www.ti.com/product/BQ25895)
  - €2.82 (https://www.digikey.nl/nl/products/detail/texas-instruments/BQ25895RTWR/5214018)
  - WQFN (RTW) (https://www.ti.com/lit/pdf/mpqf167c) – solderen met reflow
  - Tot 5A laadstroom
  - Input current limit (100 mA to 3.25 A with 50-mA resolution) to support USB2.0, USB3.0 standard and high voltage adapters (Geen USB-C)

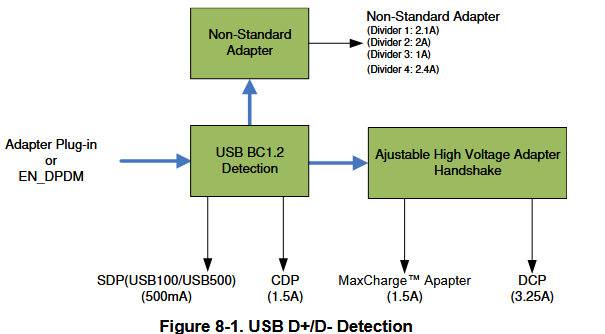
[picture p22: figure]

  - I2C verbinding
  - Integrated ADC for system monitor (voltage, temperature, charge current)
- BQ25630 (https://www.ti.com/product/BQ25630)
  - €3.2 (https://www.digikey.be/nl/products/detail/texas-instruments/BQ25630YBGR/28738812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)
  - DSBGA (YBG) (https://www.ti.com/lit/pdf/mxbg420) – zeer klein
  - Gelijkaardig aan BQ25895 (5A laadstroom, USB-detectie) met USB-C
- BQ25629 (https://www.ti.com/product/BQ25629)
  - Gelijkaardig, tot 2A, USB 2.0 en 3.0 (geen USB-C)

## 11.5 BMS uitgang

3.3V voor de meeste componenten, 5V voor een WS2812 kleurled en servomotor.

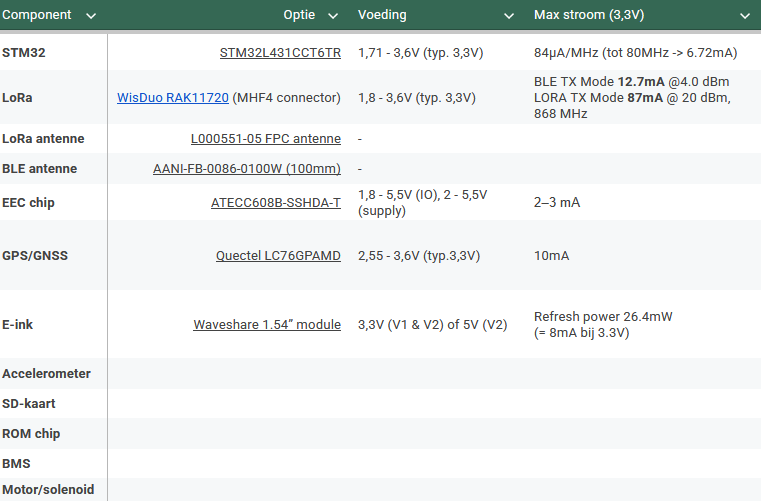
[picture p23: figure]

18650 batterijen zijn 4.2V volgeladen en kunnen veilig leeglopen tot 3V.

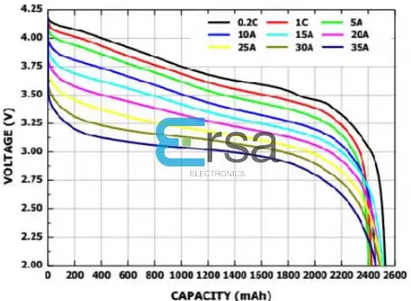
[picture p24: figure]

De Quectel GPS moet met een lineaire regulator gevoed worden voor ruis tegen te gaan. Een regulator is ~80% efficient. Een LDO (low dropout) regulator is nodig voor minimale spanningsval (bv. 200mV). De GPS werkt tot min. 2.55V, dus de batterij kan tot 3V zakken. Max stroom = 10mA.

Een buck converter is efficienter (~96%). De andere componenten zouden met een 3.3V buck kunnen gevoed worden. De buck kan klein zijn, de max. stroom zou 100-150mA zijn.

Er is ook een 5V boost converter nodig voor de WS2812 kleurled en servomotor. De servomotor (TD-8120MG (https://www.tinytronics.nl/product_files/002172_Data%20Sheet%20of%20TD-8120MG%20Digital%20Servo%20Motor.pdf)) verbruikt max. 2.1A (als hij geblokkeerd is).

De E-ink module is waarschijnlijk onbetrouwbaar onder 3.3V (bevat interne boost converters), maar kan ook met 5V gevoed worden.

- 3.3V buck-boost i.p.v. buck
  - €1-2 duurder
  - Iets minder efficient (85-93%)
- E-ink op 5V boost
  - 2-3A boost heeft waarschijnlijk meer rimpel
  - WS2812b kan ruis injecteren
  - E-ink is gevoelig voor storing, mag best niet ge-update tijdens servo gebruik en moet ontkoppeld worden met verschillende condensators

## 11.6 Opties - buck/boost/LDO

### 11.6.1 3.3V LDO

Zoekopdracht mouser (https://www.mouser.be/c/semiconductors/power-management-ics/voltage-regulators-voltage-controllers/switching-voltage-regulators/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)

- TCR3UG33A,LF (https://www.mouser.be/ProductDetail/Toshiba/TCR3UG33ALF?qs=0lQeLiL1qyaZy60Q7HF0yg%3D%3D) of TCR3UG33B,LF (https://www.mouser.be/ProductDetail/Toshiba/TCR3UG33BLF?qs=byeeYqUIh0MOLHPbjAHuLA%3D%3D)
  - 0,241 €
  - 3.3V LDO, 300mA, 140 mV dropout, 380nA ruststroom
  - WCSP4F package (zeer klein om te solderen)
- AP7368D-33RS4-7 (https://www.diodes.com/assets/Datasheets/AP7368.pdf)
  - 0,29 € (https://www.digikey.be/nl/products/detail/diodes-incorporated/AP7368D-33RS4-7/17874438)
  - 3.3V LDO, 500mA/1A
  - 60-90mV dropout (bij 3.3V 500mA)
  - 110μA ruststroom
  - Ripple Rejection 80dB at 1kHz
  - Low Output Noise, 16μVrms from 10Hz to 100kH
- MCP1711 (https://ww1.microchip.com/downloads/en/DeviceDoc/20005415D.pdf)
  - €0.43 digikey (https://www.digikey.be/nl/products/detail/microchip-technology/MCP1711T-33I-OT/5358305)
  - 3.3V LDO, 150mA
  - 170-670mV dropout
  - 600nA ruststroom, 20nA standby stroom
  - SOT-23, makkelijker te solderen

### 11.6.2 3.3V buck

- TPS62740 (https://www.ti.com/product/TPS62740)
  - €1.28 mouser (https://www.mouser.be/ProductDetail/Texas-Instruments/TPS62740DSST?qs=6E8igxPflKcEX5qfcsq2tQ%3D%3D), digikey (https://www.digikey.be/nl/products/detail/texas-instruments/TPS62740DSSR/4515200)
  - 2 MHz 300mA step-down buck DCDC converter with 360nA Iq
  - Up to 90% Efficiency at 10μA Output
  - Low Output Ripple Voltage
  - Package: WSON (DSS) (https://www.ti.com/lit/pdf/mpds336c)
- S-85S1A (https://www.ablic.com/en/doc/datasheet/switching_regulator/S85S1A_E.pdf)
  - €1.42 mouser (https://www.mouser.be/ProductDetail/ABLIC/S-85S1AB33-I6T1U?qs=y6ZabgHbY%252Bx0oX3UA0W%2F5A%3D%3D)
  - 90.5% efficiency (100µA load)
  - 260 nA quiescent current
  - SNT-A-6 (https://www.ablic.com/en/semicon/package/archive/snt-6a-pg006-a/) package

### 11.6.3 3.3V buck + LDO

- MIC2225 (https://www.microchip.com/en-us/product/MIC2225)
  - 2MHz 600mA Synchronous Buck Regulator with 300mA LDO (https://ww1.microchip.com/downloads/en/DeviceDoc/mic2225.pdf)

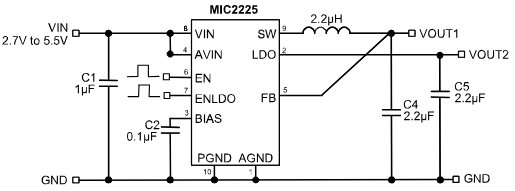
[picture p25: figure]

  - 1.8V buck, 3.3V LDO -> 1.8V is ok voor STM32, LoRa en ECC chip (accelerometer, ROM en SD module?)

### 11.6.4 3.3V buck-boost

- RAA236100, RAA236105 (https://www.mouser.be/datasheet/3/1166/1/REN_RAA236100_105_DST_20250124.pdf)
  - €1.5 mouser (https://www.mouser.be/ProductDetail/Renesas-Intersil/RAA2361052GNPHC5?qs=olJun0bQHM%2FTMxAlNSaKDw%3D%3D)
  - Zeer efficient, zeer lage ruststroom
  - 130nA input quiescent current
  - 96% peak efficiency (V IN = 3.6V; V OUT = 3.3V)
  - Output current: up to 400mA (VIN > 2.5V, V OUT = 3.3V)
  - DFN-10 package
- RT6150B (https://www.richtek.com/SaveDownload.aspx?specid=RT6150A/RT6150B)
  - €1.58 digikey (https://www.digikey.be/nl/products/detail/richtek-usa-inc/RT6150B-33GQW/6676709)
  - Tot 90% efficient
  - 800mA output
  - 60µA ruststroom, 1µA shutdown
- RT6158AWSC (https://www.mouser.be/ProductDetail/Richtek/RT6158AWSC?qs=amGC7iS6iy8gZnSqdFBonA%3D%3D)
  - €1.68 mouser
  - Tot 96% efficient
  - 5µA ruststroom
  - 2A output

### 11.6.5 5V boost

Mouser zoekopdracht (https://www.mouser.be/c/semiconductors/power-management-ics/voltage-regulators-voltage-controllers/switching-voltage-regulators/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)

Digikey zoekopdracht (https://www.digikey.be/nl/products/filter/power-management-pmic/spanningsregelaars-dc-dc-schakelende-regelaars/739)

TI power circuit designer (https://webench.ti.com/power-designer/switching-regulator/select)

- TPS61253AYFFT (https://www.ti.com/lit/ds/symlink/tps61253e.pdf?ts=1774602914401)
  - €1.18 mouser (https://www.mouser.be/ProductDetail/Texas-Instruments/TPS61253AYFFR?qs=u4fy%2FsgLU9MozJblstQuaA%3D%3D)
  - IOUT 1500mA (startup), 4A (SW valley current limit)
  - 42μA quiescent current (<1.3µA shutdown)

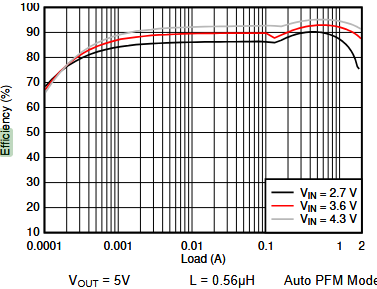
[picture p26: figure]

  - DSBGA-9 (https://www.ti.com/lit/ml/mxbg144b/mxbg144b.pdf?ts=1774606994625) ball grid array – klein om te solderen
- TPS61022 (https://www.ti.com/lit/ds/symlink/tps61022.pdf?ts=1774955467241)
  - € 1.75 mouser (https://www.mouser.be/ProductDetail/Texas-Instruments/TPS61022RWUR?qs=vLWxofP3U2zlxrk4cD0iFA%3D%3D)
  - In: 0.5 V to 5.5 V, out: 2.2 V to 5.5 V
  - 8A switch current, 3A output
  - Schema voor 5V uitgang, 95.7% efficiëntie, 1.02MHz, ~$2.85

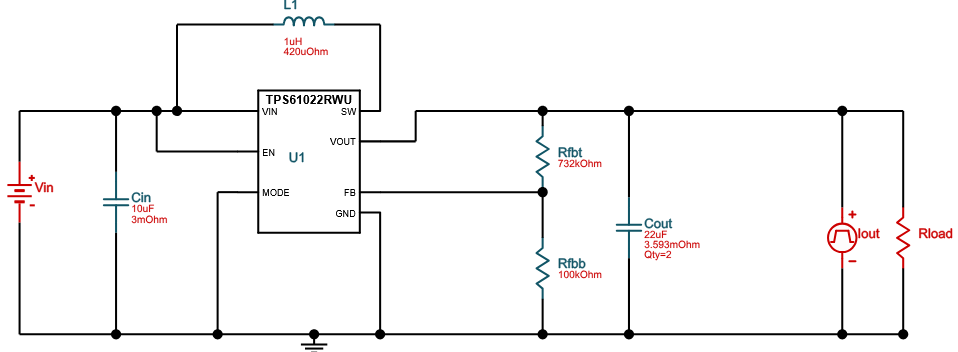
[picture p27: figure]
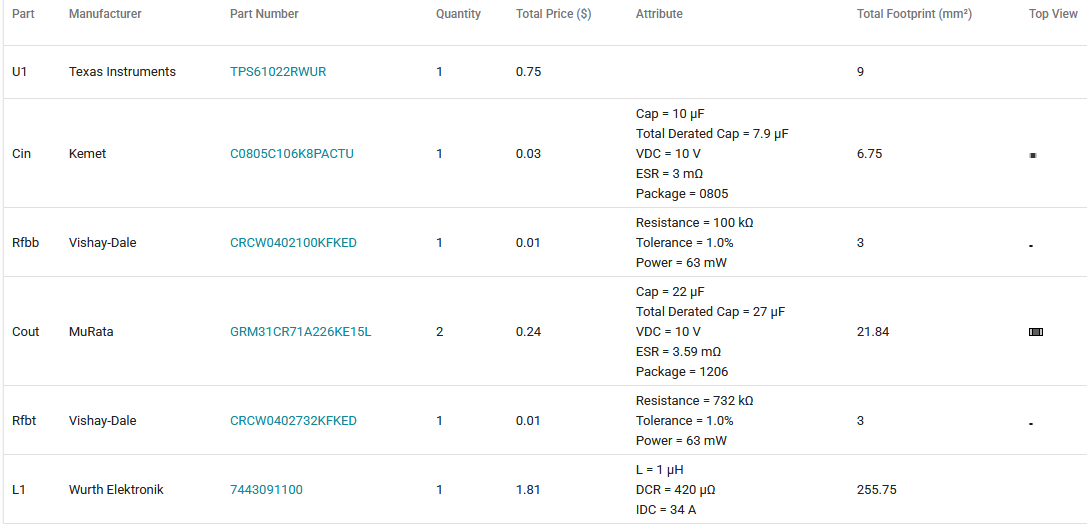
[picture p28: figure]

## 11.7 Keuze

Lader: BQ25630 (https://www.ti.com/product/BQ25630)

- Digikey (https://www.digikey.nl/nl/products/detail/texas-instruments/BQ25895RTWR/5214018) Mouser (https://www.mouser.be/ProductDetail/Texas-Instruments/BQ25895RTWR)

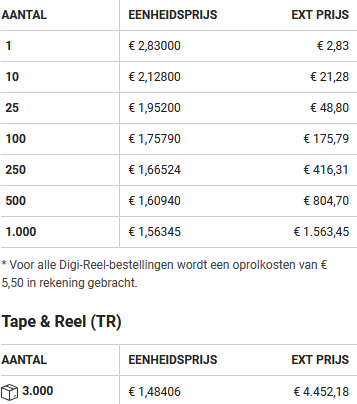
[picture p29: figure]
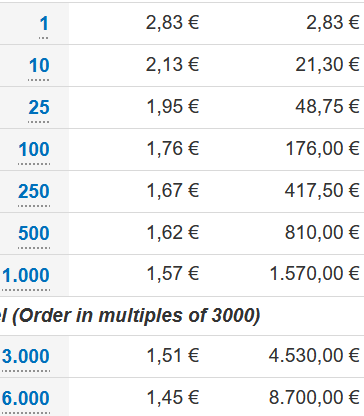
[picture p30: figure]

- I2C 1cell 5A buck battery charger with high input voltage and 3.1-A boost with HVDCP enabled.

Buck-boost (voor finaal ontwerp): RAA236105 (https://www.mouser.be/ProductDetail/Renesas-Intersil/RAA2361052GNPHC5?qs=olJun0bQHM%2FTMxAlNSaKDw%3D%3D)

- mouser (https://www.mouser.be/ProductDetail/Renesas-Intersil/RAA2361052GNPHC5?qs=olJun0bQHM%2FTMxAlNSaKDw%3D%3D) (niet in voorraad) digikey (https://www.digikey.be/nl/products/detail/renesas-electronics-corporation/RAA2361052GNP-HC5/25811418) (niet in voorraad)

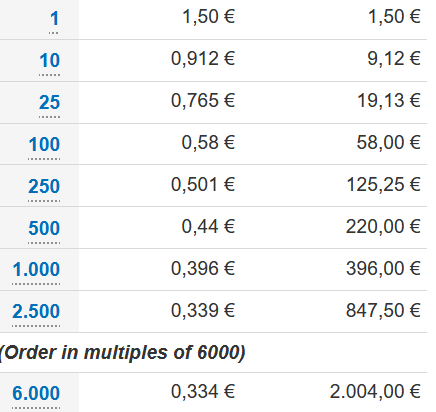
[picture p31: figure]
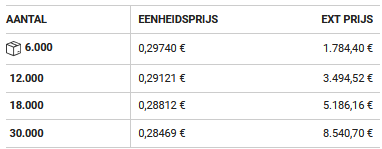
[picture p32: figure]

- 130nA input quiescent current
- 96% peak efficiency (V IN = 3.6V; V OUT = 3.3V)
- Output current: up to 400mA (VIN > 2.5V, V OUT = 3.3V)

Buck-boost (voor prototype): RT6158AWSC (https://www.mouser.be/ProductDetail/Richtek/RT6158AWSC?qs=amGC7iS6iy8gZnSqdFBonA%3D%3D)

  - €1.68 mouser
  - Tot 96% efficient
  - 5µA ruststroom
  - 2A output

LDO: TCR3UG33A,LF (https://www.mouser.be/ProductDetail/Toshiba/TCR3UG33ALF?qs=0lQeLiL1qyaZy60Q7HF0yg%3D%3D) (met auto-discharge) of TCR3UG33B,LF (https://www.mouser.be/ProductDetail/Toshiba/TCR3UG33BLF?qs=byeeYqUIh0MOLHPbjAHuLA%3D%3D) (zonder auto-discharge)

- € 0.241
- 3.3V LDO, 300mA, 140 mV dropout, 380nA ruststroom

5V boost:

- TPS61253 (https://www.ti.com/lit/ds/symlink/tps61253e.pdf?ts=1774602914401)
  - mouser (https://www.mouser.be/c/?q=TPS61253) , digikey (https://www.digikey.be/nl/products/filter/spanningsregelaars-dc-dc-schakelende-regelaars/739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)

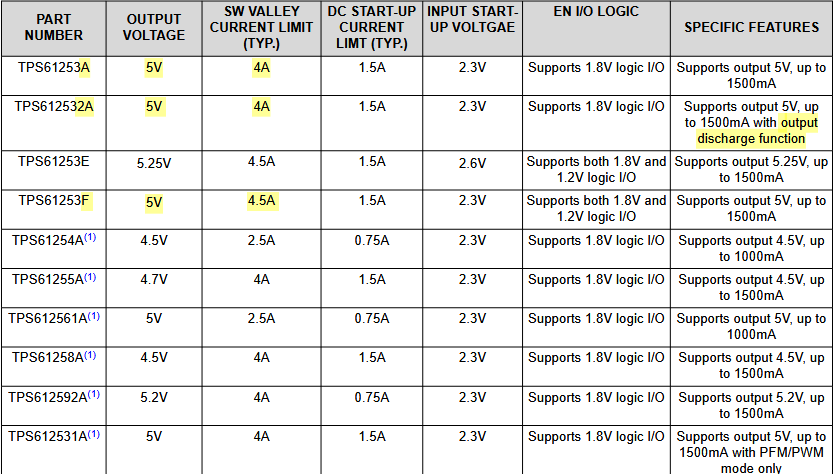
[picture p33: figure]

  - TPS61253A: mouser (https://www.mouser.be/ProductDetail/Texas-Instruments/TPS61253AYFFT?qs=u4fy%2FsgLU9N%2FvtqNk3aM7Q%3D%3D), digikey (https://www.digikey.com/en/products/detail/texas-instruments/TPS61253AYFFR/7653234) (4A Isw)
  - TPS612532A: mouser (https://www.mouser.be/ProductDetail/Texas-Instruments/TPS612532AYFFR?qs=81r%252BiQLm7BToZysNiA2fsw%3D%3D), digikey (https://www.digikey.com/en/products/detail/texas-instruments/TPS612532AYFFR/13563025) (4A Isw, auto-discharge)
  - TPS61253F: mouser (https://www.mouser.be/ProductDetail/Texas-Instruments/TPS61253FYFFR?qs=fQuHqd5sRUjoF7f8WiF7wg%3D%3D), digikey (https://www.digikey.com/en/products/detail/texas-instruments/TPS61253FYFFR/29174815) (4.5A Isw, niet in voorraad bij mouser, goedkoopste bij digikey)

# 12 Motor/solenoide

We kiezen deze servo: TD-8120MG (https://www.tinytronics.nl/en/mechanics-and-actuators/motors/servomotors/td-8120mg-waterproof-digital-servo-20kg)

- Vcc: 5V
- PWM gestuurd (3-5V)

De pin om het slot dicht te klikken is verbonden met een servomotor, langs een veer. De servo motor heeft 5V nodig en wordt aangesloten op de 5V boost module. Met een sense weerstand kunnen we overstroom meten om te zien of de servo geblokkeerd is, en we kunnen de servo uitschakelen door de boost converter uit te schakelen (enable pin).

# 13 Kleur led

Addresseerbare RGB LEDs zoals WS2812b zijn gemakkelijk, maar werken alleen op 5V omdat de spanningsval van een blauwe LED 3.3V is of hoger. Deze zou moeten aangesloten worden op de 5V boost module, maar deze is voor de servomotor en zou niet altijd actief zijn.

Als alternatief kunnen we een gewone RGB kleurled gebruiken met gemeenschappelijke cathode of anode. Met gemeenschappelijke kathode gaat de led aan als de poort logisch hoog is en levert de STM32 stroom (source). Met gemeenschappelijke anode gaat de led aan als de poort logisch laag is, dan neemt de STM32 stroom (sink).

De LEDS kunnen met weerstanden rechtstreeks op GPIO’s van de STM32 worden aangesloten, als de stroom laag genoeg gelimiteerd is. Een GPIO pin kan max 20mA aan, en alle I/O stromen samen mogen max 100mA zijn (datasheet STM32L4 p.87), ik zou de stroom tussen 5 en 10mA houden. Voor meer helderheid en stroom zouden best transistors gebruikt worden, maar dat zal waarschijnlijk niet nodig zijn.

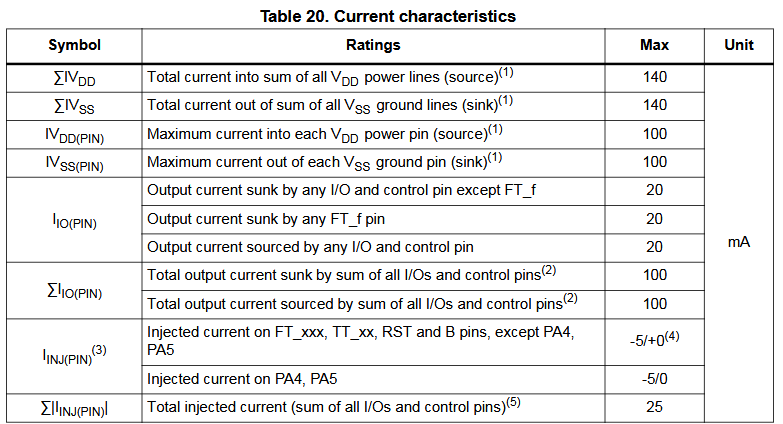
[picture p34: figure]

De weerstand kan bepaald worden met de wet van ohm:

R = (VGPIO−Vf)/I

Er zijn 6 mogelijke kleuren en wit door de GPIO’s laag of hoog te zetten. Andere kleuren of helderheid is ook mogelijk als PWM gebruikt wordt.

## 13.1 Opties

Mouser zoekopdracht (https://www.mouser.be/c/optoelectronics/led-lighting/leds-light-emitting-diodes/multi-color-leds/?q=rgb%20led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)

- ASMB-KTF0-0A306 (https://4donline.ihs.com/images/VipMasterIC/IC/AVGO/AVGO-S-A0004511384/AVGO-S-A0004511384-1.pdf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)
  - 0,335 € mouser (https://www.mouser.be/ProductDetail/Broadcom-Avago/ASMB-KTF0-0A306?qs=j%252B1pi9TdxUYIaJsf%252B0lh6A%3D%3D)
  - SMD

- If - Forward Current: | R 10 mA, G 15 mA, B 15 mA
- Vf - Forward Voltage: | R 2 V, G 2.95 V, B 2.85 V

  - RGB - common anode – laag gestuurd.
  - Weerstanden nodig voor 8mA (E24):
    - (3.3V – 2V) / 8mA = 162.5 Ω -> 160 Ω
    - (3.3V - 2.95V) / 8mA = 43.75 Ω -> 43 Ω
    - (3.3V - 2.85V) / 8mA = 56.25 Ω -> 56 Ω
- XL-3227SURUGC (https://mm.digikey.com/Volume0/opasdata/d220001/medias/docus/8903/XL-3227SURUGC.pdf)
  - €0.03718 digikey (https://www.digikey.be/nl/products/detail/xinglight/XL-3227SURUGC/25673368)
  - Rood, groen
  - SMD
  - If – forward current: 20mA
  - Vf- Forward Voltage: Rood: 1.9 – 2.3V, Groen: 2.6 – 3.4V
  - Weerstanden nodig voor 8mA (E24):
    - (3.3V – 2.1V) / 8mA = 150 Ω -> 150 Ω
    - (3.3V – 3.1V) / 8mA = 25 Ω -> 24 Ω
  - Min. 3000
- BL-BEG204-7-E (https://www.americanbrightled.com/pdffiles/led-components/through-hole/BL-BEG204-7-E.pdf)
  - €0.15 digikey (https://www.digikey.be/nl/products/detail/american-bright-optoelectronics-corporation/BL-BEG204-7-E/22486902)
  - 5mm THT LED
  - Rood, groen
  - If – forward current: 20mA
  - Vf- Forward Voltage: Rood: 2V (max 2.6V), Groen: 2.2 (max 2.6V)
  - Weerstanden nodig voor 8mA (E24):
    - (3.3V – 2V) / 8mA = 162.5 Ω -> 160 Ω
    - (3.3V – 2.2V) / 8mA = 137.5 Ω -> 130 Ω

## 13.2 Keuze

- BL-BEG204-7-E (https://www.americanbrightled.com/pdffiles/led-components/through-hole/BL-BEG204-7-E.pdf): 5mm THT rood-groen LED met 160Ω en 130Ω weerstand.

# 14 Hall effect sensoren

Magneetsensoren op het uiteinde van de beugel en pin van het slot om te detecteren of het slot dicht is.

Silicon labs maakt sensoren met tamper indication, die een te hoog magnetisch veld niet registreren. De volledige Si720x serie (https://www.silabs.com/sensors/magnetic/si720x) heeft de status Not Recommended for New Designs (NRND). 3D hall effect sensoren die x-y en z as registreren kunnen ook gebruikt worden tegen tampering, maar zijn iets duurder (€1). Tamper indicatie is waarschijnlijk niet nodig als twee hall sensoren gebruikt worden.

## 14.1 Opties

- TCS40DPR,LF (https://toshiba.semicon-storage.com/info/docget.jsp?did=30107&prodName=TCS40DPR)
  - €0.15 digikey (https://www.digikey.be/nl/products/detail/toshiba-semiconductor-and-storage/TCS40DPR-LF/5012764)
  - SMD
  - 12.8µA average current
- SI7201-B-40-IVR (https://www.silabs.com/documents/public/data-sheets/si720x-data-sheet.pdf)
  - €0.87 digikey (https://www.digikey.be/nl/products/detail/silicon-labs/SI7201-B-40-IVR/10283814)
  - SMD
  - tamper indication (pin going back to its zero field level at high magnetic field)
  - Low 400 nA Typical Current Consumption at 5 samples per second
  - Not Recommended for New Designs (NRND)
- SL1623SH (https://mm.digikey.com/Volume0/opasdata/d220001/medias/docus/7181/SL1623SH%20SOT-23.pdf)
  - €0.13 digikey
  - SMD
  - Unipolair (N-pole): SL1623SH (https://www.digikey.be/nl/products/detail/shenzhen-slkormicro-semicon-co-ltd/SL1623SH/27519071)

Unipolair (S-pole): SL1613SH (https://www.digikey.be/nl/products/detail/shenzhen-slkormicro-semicon-co-ltd/SL1613SH/27519090)

Omnipolair: SL1603SH (https://www.digikey.be/nl/products/detail/shenzhen-slkormicro-semicon-co-ltd/SL1603SH/27519072)

  - 1.6µA

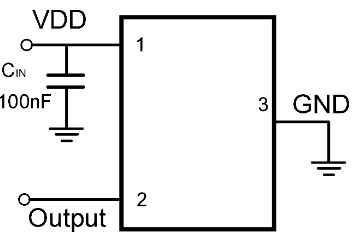
[picture p35: figure]

- CT8132EK-HS3 (https://www.mouser.be/datasheet/3/3802/1/CT813x_Datasheet.pdf)
  - €0.361 (min. 18000)
  - Zeer lage stroom: 145 nA
  - SMD
  - Omnipolair

THT is iets duurder:

- DRV5032FBLPGM (https://www.ti.com/lit/gpn/drv5032)
  - €0.41 mouser (https://www.mouser.be/ProductDetail/Texas-Instruments/DRV5032FBLPGM?qs=OlC7AqGiEDmjWFVLQlMDAA%3D%3D)
  - Omnipolair
  - – 5Hz version: 0.54μA

– 20Hz versions: 1.3μA

– 80Hz version: 5.2μA

- DRV5032DULPGM (https://www.ti.com/lit/gpn/drv5032)
  - €0.31 mouser (https://www.mouser.be/ProductDetail/Texas-Instruments/DRV5032DULPGM?qs=OlC7AqGiEDk9MwfBkgsRPw%3D%3D)
  - Unipolair

## 14.2 Keuze

Voorstel: SL1623SH (https://www.digikey.be/nl/products/detail/shenzhen-slkormicro-semicon-co-ltd/SL1623SH/27519071) en SL1613SH (https://www.digikey.be/nl/products/detail/shenzhen-slkormicro-semicon-co-ltd/SL1613SH/27519090)

- Unipolair, noord en zuidpool. Kan niet allebei met externe magneet geactiveerd worden.
- €0.13 digikey
- SMD
- 1.6µA

# 15 ST-link

Er wordt gebruik gemaakt van een externe ST-link om de STM32 te programmeren en debuggen, dat kan verbonden worden op een ST-link header.

## 15.1 Debug protocols

Er zijn verschillende protocollen beschikbaar om te debuggen en voor firmware update. De STM32L4 ondersteunt SWD en JTAG.

### 15.1.1 SWD (Serial Wire Debug)

2 draden (SWDIO en SWCLK) voor firmware flashen, breakpoints instellen, geheugen inspecteren en toegang krijgen tot een debugconsole. Op STM32L4 is SWDIO verbonden met PA13 en SWDCLK met PA14.

### 15.1.2 JTAG (Joint Test Action Group)

4-5 draden: JTMS/SWDIO (PA13), JTCK/SWCLK (PA14), JTDI (PA15), JTDO (PB3), and NJTRST (PB4). Dezelfde pinnen als SWD (PA13 en PA14) worden hierbij gebruikt. JTAG is actief als de STM32 opstart, maar de debugger wisselt vaak naar SWD.

### 15.1.3 SWIM (Single Wire Interface Module)

Sommige ST-links ondersteunen SWIM, maar de STM32L4 maakt daar geen gebruik van.

## 15.2 Seriële interface

Een virtual COM port wordt gebruikt voor een seriële interface met real-time logging en instelcommando’s. De seriële interface kan via de USB uitgang, rechtstreeks met DFU (direct firmware update) pinnen, maar dat is een veiligheidsrisico omdat de STM32 dan ook zou kunnen geprogrammeerd worden via de USB-uitgang. Ik dacht eerst om in de plaats een UART-poort te verbinden naar USB met een UART-to-USB bridge, maar de STM32 kan zo ook geprogrammeerd worden en is ook een veiligheidsrisico.

Een ST-link V2 heeft geen mogelijkheid voor Virtual COM port (VCP). Een ST-link V3 wel.

## 15.3 Opties

Overview of ST-link derivatives (https://www.st.com/resource/en/technical_note/tn1235-overview-of-stlink-derivatives-stmicroelectronics.pdf)

- ST-link V2 clone (€5.5 tinytronics) (https://www.tinytronics.nl/en/communication-and-signals/serial/usb/st-link-v2-stm8stm32-compatible)
  - Goedkoop
  - Firmware update, JTAG/serial wire debugging (SWD)
  - Geen Virtual COM port (VCP)
  - Voor de seriële interface kan gebruik gemaakt worden van een externe TTL USB to serial converter, waarbij UART verbonden wordt met pin headers en niet via de USB-uitgang.

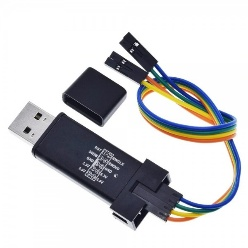
[picture p36: figure]
ST-LINK V2 - STM8/STM32 - Compatible

- STLINK-V3MINIE (https://www.st.com/en/development-tools/stlink-v3minie.html?ecmp=tt9470_gl_link_feb2019&rt=an&id=AN6382)
  - €21.4 mouser (https://www.mouser.be/ProductDetail/STMicroelectronics/STLINK-V3MINIE?qs=MyNHzdoqoQKcLQe5Jawcgw%3D%3D)
  - €19.21 Farnell (https://be.farnell.com/en-BE/stmicroelectronics/stlink-v3minie/debugger-prog-probe-32bit-arm/dp/3953430)
  - Firmware update, JTAG/serial wire debugging (SWD) and SWV (Serial Wire Viewer)
  - Virtual COM port (VCP) up to 15 Mbps through one UART
  - 1.27 mm pitch STDC14 debug connector with STDC14 to STDC14 flat cable
  - 2.0 mm pitch on-board pads for BTB (Board-to-board) card edge connector

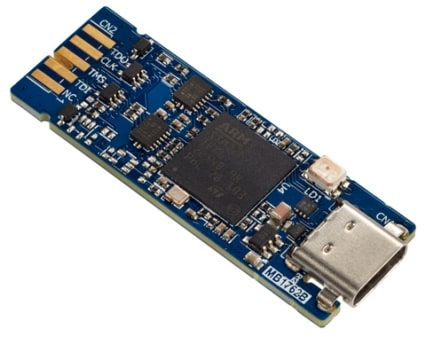
[picture p37: figure]
STLINK-V3 compact in-circuit debugger and programmer for STM32

- STLINK-V3MODS (https://www.st.com/en/development-tools/stlink-v3mods.html?ecmp=tt9470_gl_link_feb2019&rt=tn&id=TN1235)
  - €10.32 mouser (https://www.mouser.be/ProductDetail/STMicroelectronics/STLINK-V3MODS?qs=%252B6g0mu59x7IGXEnyh258yQ%3D%3D)
  - Firmware update, JTAG/serial wire debugging (SWD) and SWV (Serial Wire Viewer)
  - Virtual COM port (VCP) up to 15 Mbps through one UART, and bridge interfaces (SPI, I²C, CAN, and GPIOs)
  - Kan rechtstreeks op de PCB gesoldeerd worden

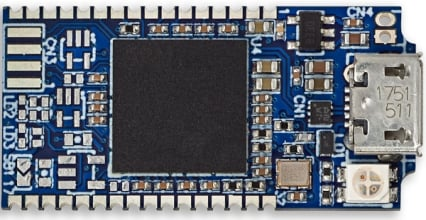
[picture p38: figure]
STLINK-V3MODS board photo

- STLINK-V3PWR (https://www.st.com/en/development-tools/stlink-v3pwr.html?ecmp=tt9470_gl_link_feb2019&rt=tn&id=TN1235)
  - € 134,76 digikey (https://www.digikey.nl/nl/products/detail/stmicroelectronics/STLINK-V3PWR/18110505)
  - Firmware update, JTAG/serial wire debugging (SWD) and SWV (Serial Wire Viewer)
  - UART interface on Virtual COM port (VCP) with frequency up to 12 MHz
  - Multipath bridge USB to SPI/I²C/CAN/GPIOs
  - Programmable voltage source from 1.6 to 3.6 V
    - With dynamic current measurement (nA to 500 mA)
    - Output current rating 500 mA
  - Auxiliary output voltage source from 1.6 to 3.6 V under up to 2 A
  - Three STDC14 to MIPI10 / STDC14 / MIPI20 flat cables with 1.27 mm pitch connectors

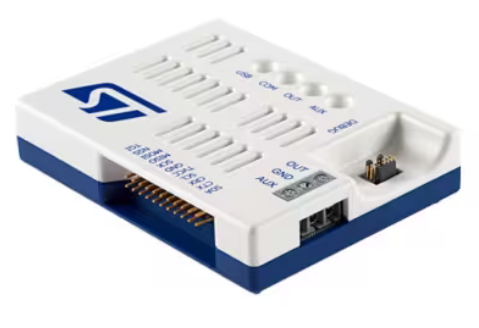
[picture p39: figure]

- STLINK-V3SET
  - (https://www.st.com/resource/en/user_manual/um2448-stlinkv3set-debuggerprogrammer-for-stm8-and-stm32-stmicroelectronics.pdf)36,89 € mouser (https://www.mouser.be/ProductDetail/STMicroelectronics/STLINK-V3SET?qs=qSfuJ%252Bfl%2Fd5d4WYsOW6M6w%3D%3D)
  - Firmware update, JTAG/serial wire debugging (SWD) and SWV (Serial Wire Viewer)
  - SWIM interface
  - Virtual COM port (VCP) up to 15 Mbps
  - Multipath bridge USB to SPI/UART/I²C/CAN/GPIOs

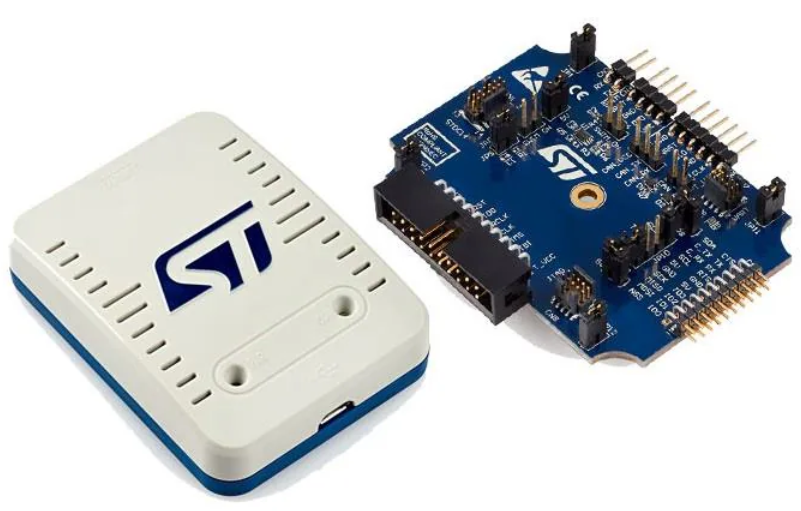
[picture p40: figure]

## 15.4 Keuze

Voorstel: STLINK-V3MINIE (https://www.st.com/en/development-tools/stlink-v3minie.html?ecmp=tt9470_gl_link_feb2019&rt=an&id=AN6382)

- €21.4 mouser (https://www.mouser.be/ProductDetail/STMicroelectronics/STLINK-V3MINIE?qs=MyNHzdoqoQKcLQe5Jawcgw%3D%3D)
- Kan rechtstreeks in deze connector: 009159010603906 card edge connector (https://www.mouser.be/datasheet/3/5926/1/9159_600.pdf) (€1.21 mouser (https://www.mouser.be/ProductDetail/KYOCERA-AVX/009159010603906?qs=ST9lo4GX8V1Mnrfaz2Mt1w%3D%3D))
- Of 1.27 mm pitch STDC14 debug connector:

FTSH-107-01-L-D-K (https://www.mouser.be/datasheet/3/85/1/ftsh_th.pdf) (€3.01 mouser (https://www.mouser.be/ProductDetail/Samtec/FTSH-107-01-L-D-K?qs=%252BZP6%2F%252BtExtDf9U3LcTl7MA%3D%3D))

# 16 Samenvatting keuzes

# 17 BOM

Zie google sheets:

Bikera fietsslot PCB componenten MCU: STM32

Bikera fietsslot PCB componenten LoRa

Bikera fietsslot PCB componenten Antenne

Bikera fietsslot PCB componenten ECC chip
