krampslaag/Bikera/Thesis bijlagen/Architectuurschema_Drawio_v3.pdf

# MCU

UART0 | GPS-GNSS

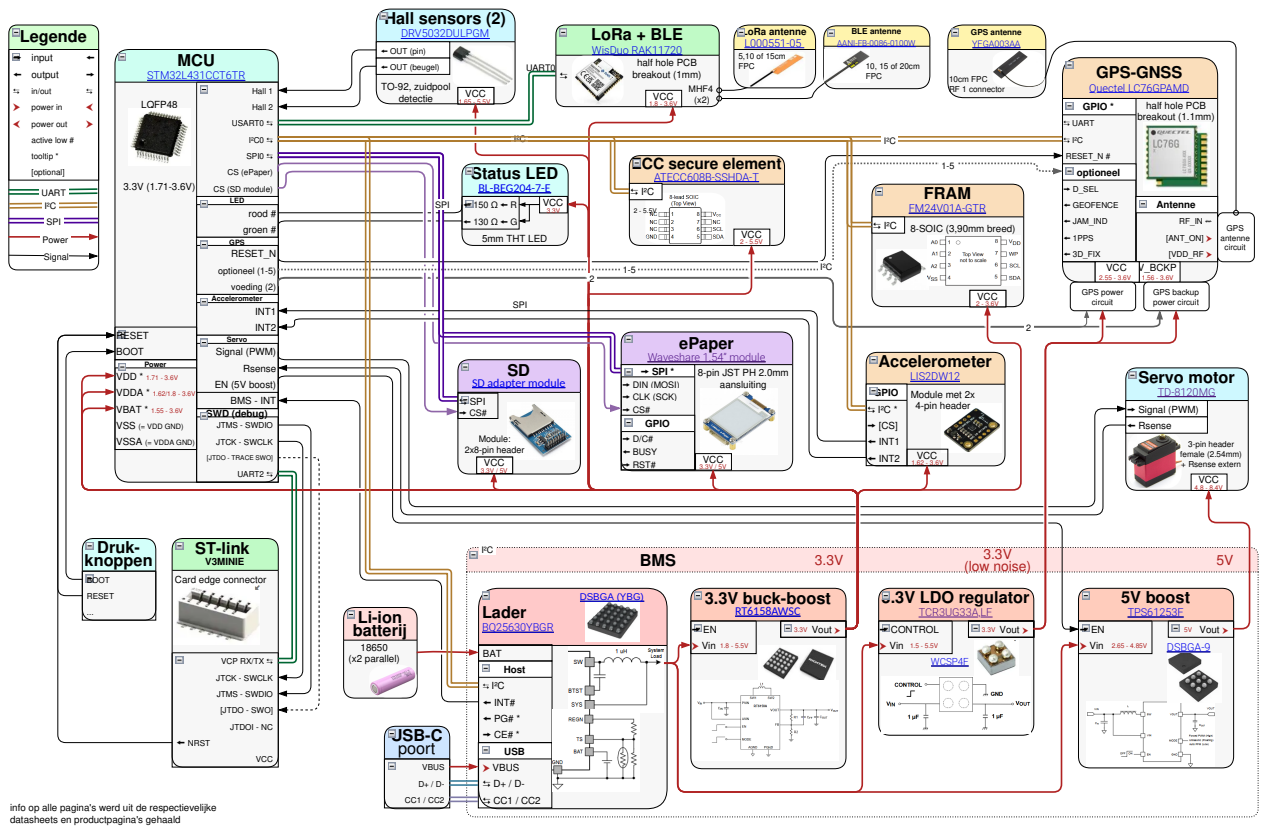
[picture p41: page 1]
STM32L431CCT6TR; Hall 1 Hall 2 USART0 ⮀ I²C0 ⮀ SPI0 ⮀ CS (ePaper) CS (SD module) LED; rood # groen # GPS RESET_N optioneel (1-5) voeding (2) Accelerometer INT1 INT2; Servo Signal (PWM) Rsense EN (5V boost) BMS - INT SWD (debug) JTMS - SWDIO JTCK - SWCLK; LQFP48; Power; RESET BOOT; Quectel LC76GPAMD GPIO *; ⮀ UART ⮀ I²C RESET_N # optioneel; 🠚 D_SEL 🠘 GEOFENCE 🠘 JAM_IND 🠘 1PPS 🠘 3D_FIX; Antenne; RF_IN ⇜ [ANT_ON] ⮞ [VDD_RF ⮞ V_BCKP 1.56 - 3.6V; VCC 2.55 - 3.6V; ePaper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

half hole PCB

breakout (1.1mm)

ECC secure element
ATECC608B-SSHDA-T (https://www.digikey.be/nl/products/detail/microchip-technology/ATECC608B-SSHDA-T/13415162)
⮀ I²C

SD adapter module (https://www.tinytronics.nl/en/data-storage/modules/sd-card-adapter-module-3.3v-5v)
⮀ SPI

8-pin JST PH 2.0mm
aansluiting

VDD * 1.71 - 3.6V
VDDA * 1.62/1.8 - 3.6V
VBAT * 1.55 - 3.6V
VSS (= VDD GND)
VSSA (= VDDA GND)

[JTDO - TRACE SWO]
UART2 ⮀

ST-link
V3MINIE
Card edge connector

VCP RX/TX ⮀
JTCK - SWCLK
JTMS - SWDIO
[JTDO - SWO]
JTDOI - NC

info op alle pagina's werd uit de respectievelijke
datasheets en productpagina's gehaald

MCU: STM32L431CCT6TR (https://be.farnell.com/stmicroelectronics/stm32l431cct6tr/mcu-32bit-80mhz-lqfp-48/dp/3365485RL)

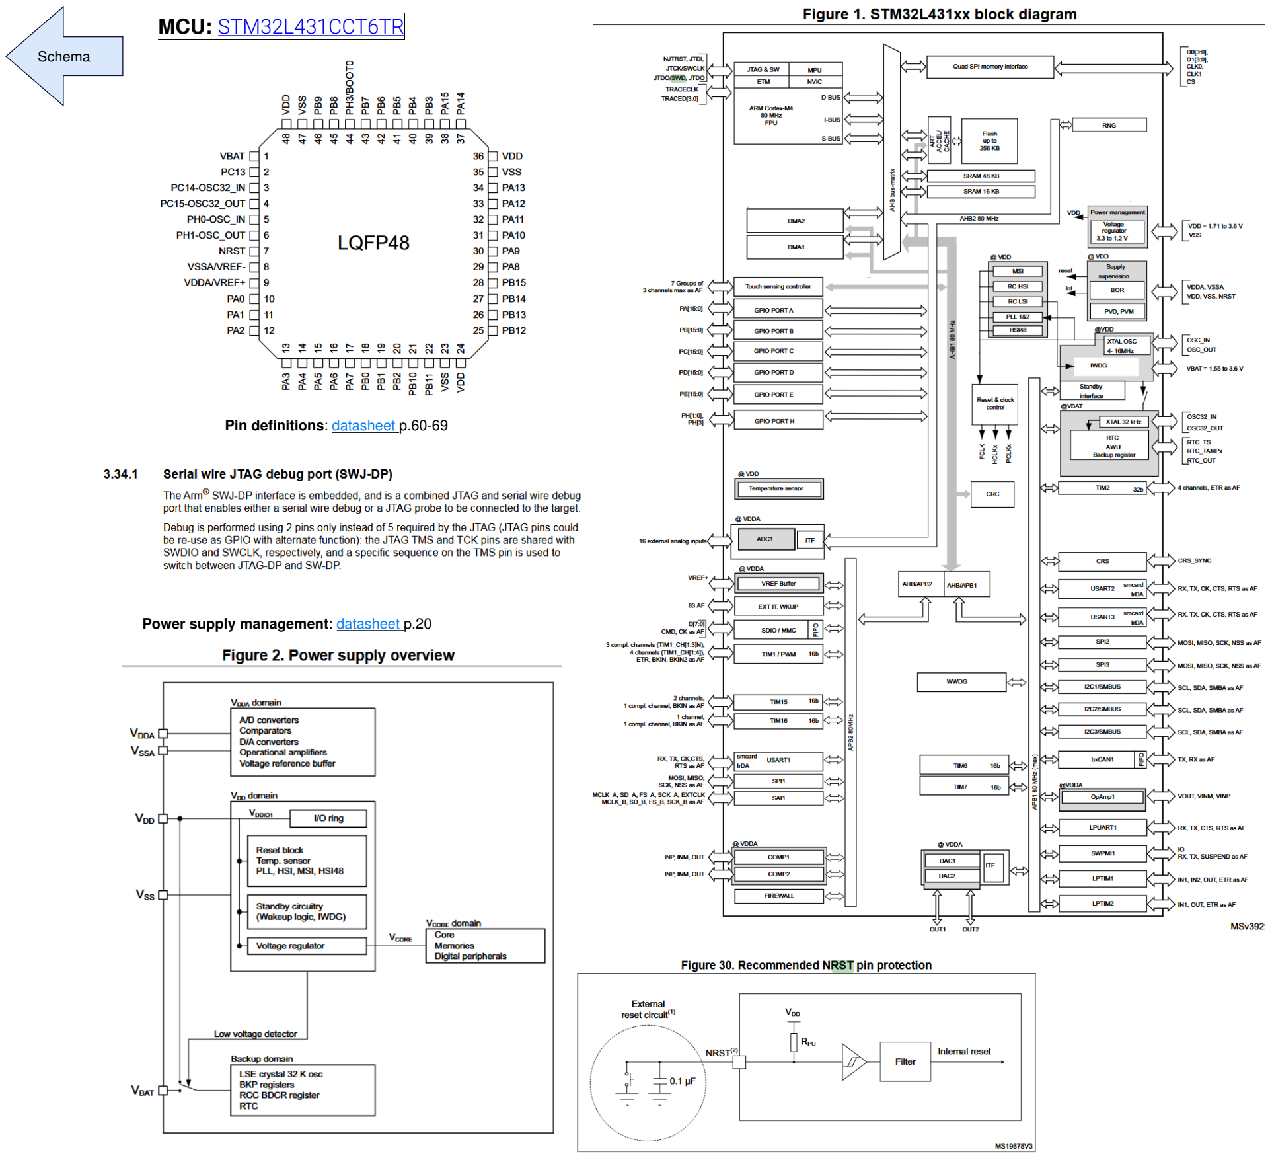
[picture p42: page 2]

Pin definitions: datasheet p.60-69

Power supply management: datasheet p.20 (https://www.st.com/resource/en/datasheet/stm32l431cb.pdf)

Schema

- Operating Voltage VCC: min.1.8 typ.3.3 max.3.6 Volts (V)
- Operating Current:
- BLE TX Mode **12.7mA** @4.0 dBm
- LORA TX Mode **87mA** @ 20 dBm, 868 MHz
- Sleep current: 2.37µA
- I²C, SPI & UART
- default = **UART0** (AT commands en FW updates)
default 115200 baud, 8 data bits, 1 stop bit, no parity
debug pinnen op UART0 (RAK kan ook met pc communiceren ([WisToolBox](https://docs.rakwireless.com/product-categories/software-tools/wistoolbox/overview))
evt. UART met USB rechtstreeks? (multiplex via jumper pins)
- 2x MHF-4
- [AT commands: RAKwireless Unified Interfave V3 (RUI3)](https://docs.rakwireless.com/product-categories/software-apis-and-libraries/rui3/overview/)
- interfaced with an external host via [AT command mode (default)](https://docs.rakwireless.com/product-categories/software-apis-and-libraries/rui3/at-command-manual/)
- custom serial interface can be created by the user using [Custom Mode](https://docs.rakwireless.com/product-categories/software-apis-and-libraries/rui3/custom-mode/)
- AT commands ook via I2C en SPI? Of worden deze alleen gebruikt bij custom firmware (RAK als master)?

Antennes: MHF4
Make sure that an antenna is always connected. Using these transceivers without an antenna can damage the module

# LoRa + BLE

# WisDuo RAK11720 Schema

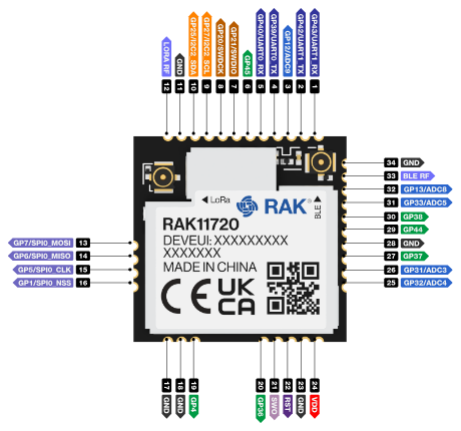
[picture p43: figure]

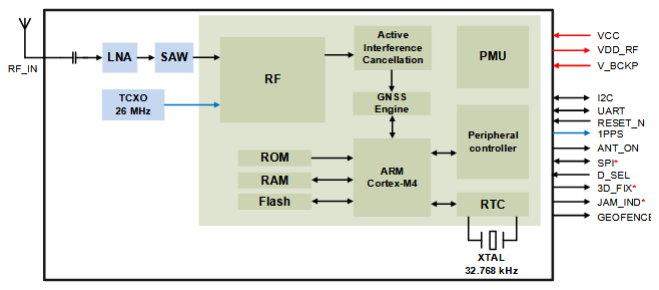
[picture p44: figure]
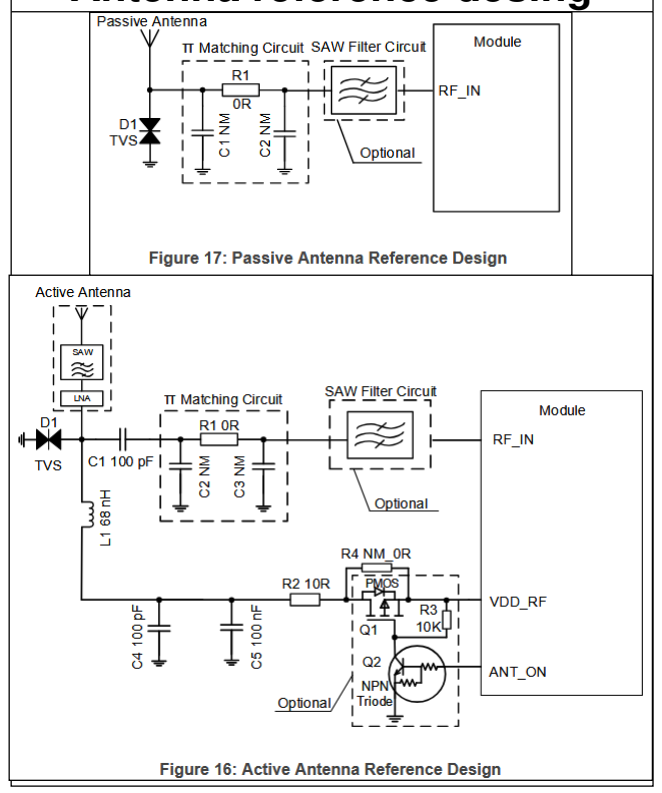
[picture p45: figure]
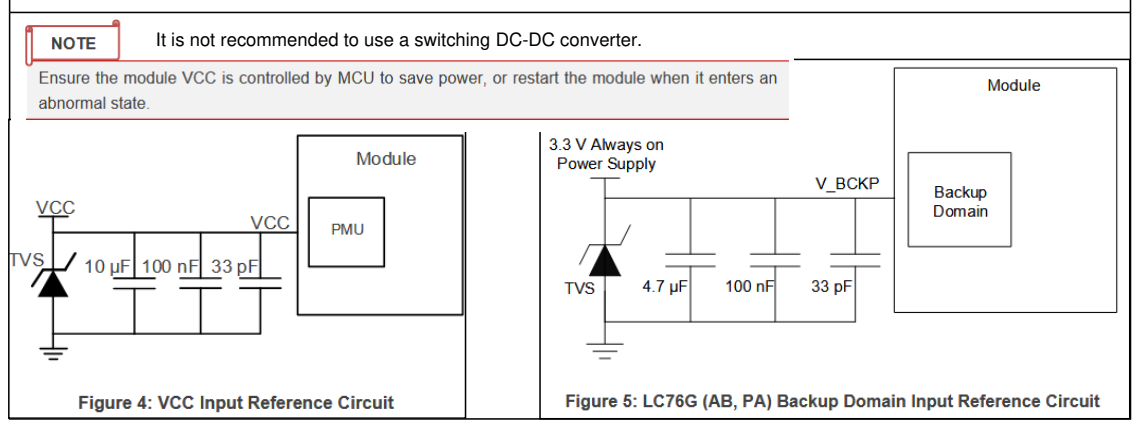
[picture p46: figure]

- Power (default constellations) (https://www.mouser.be/ProductDetail/Quectel/LC76GPAMD?qs=vvQtp7zwQdMfDuCTmjRUww%3D%3D) Normal Operation: (https://www.mouser.be/ProductDetail/Quectel/LC76GPAMD?qs=vvQtp7zwQdMfDuCTmjRUww%3D%3D)
**10 mA** (33 mW) @ Acquisition 10 mA (33 mW) @ Tracking
Power Saving Modes:
5.5 mA (18.15 mW) @ ALP Mode 13 μA (42.9 μW) @ Backup Mode
- Power (GPS + GLONASS):
Normal Operation:
9 mA (29.7 mW) @ Acquisition 9 mA (29.7 mW) @ Tracking
Power Saving Modes:
4.6 mA (15.18 mW) @ ALP Mode

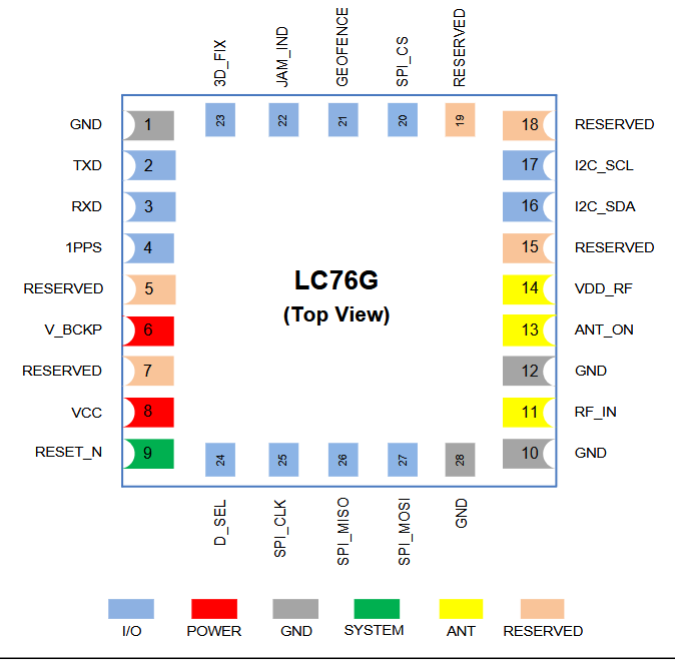
[picture p47: figure]
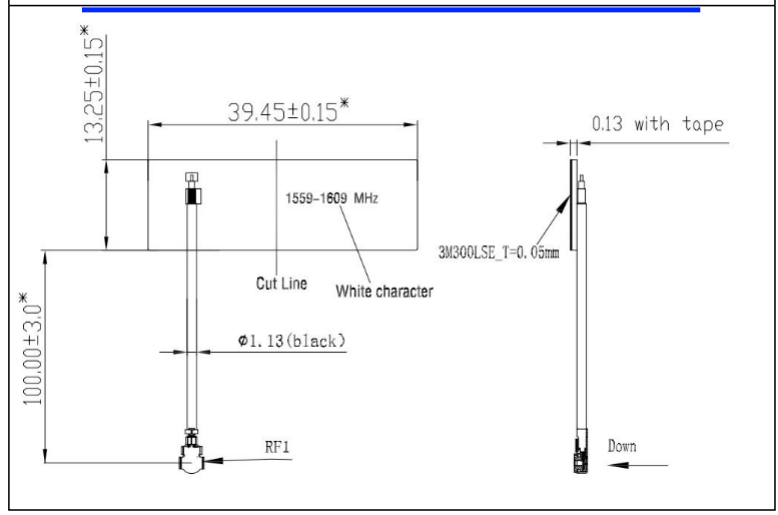
[picture p48: figure]

Dimensions | Antenna reference desing

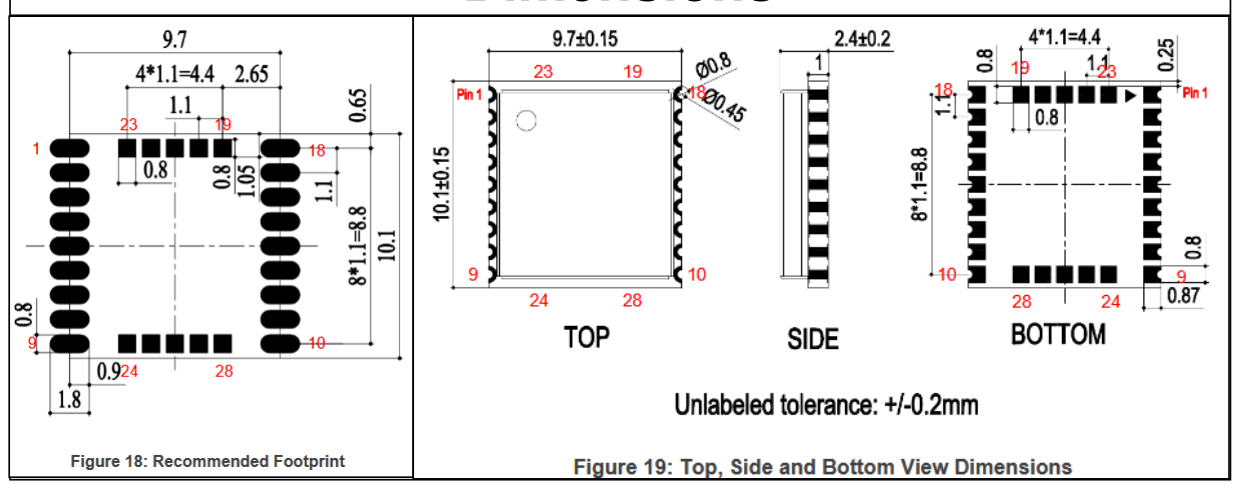
[picture p49: figure]

Power It (https://www.mouser.be/ProductDetail/Quectel/LC76GPAMD?qs=vvQtp7zwQdMfDuCTmjRUww%3D%3D) is not recommended to use a switching DC-DC converter.

Schema | GPS-GNSS Quectel LC76GPAMD | FPC antenne: YFGA003AA

ePaper module STM32 (demo)
VCC | 3.3V | 3.3V/5V
GND | GND

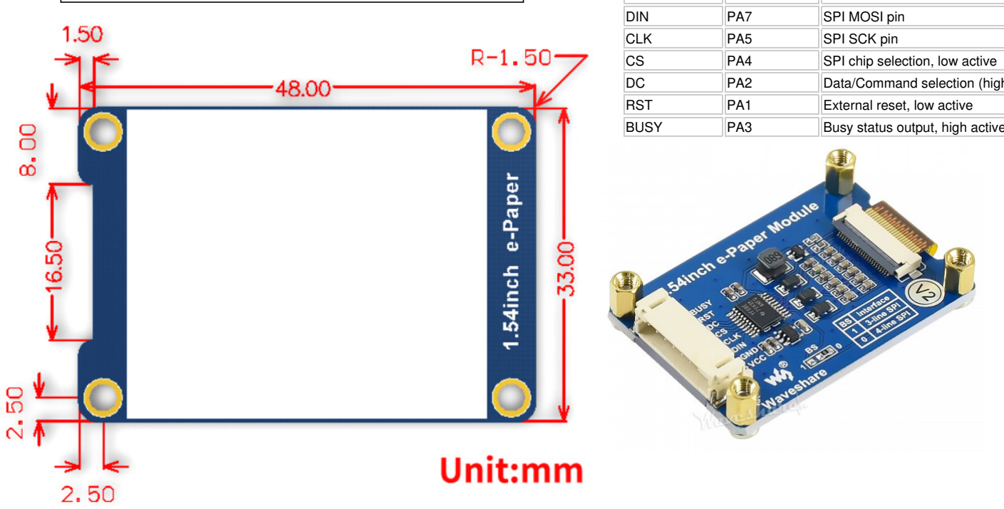
[picture p50: figure]
DIN; SPI MOSI pin; CLK; SPI SCK pin; SPI chip selection, low active; RST; External reset, low active

DC | PA2 | Data/Command selection (high for data, low for command)
BUSY | PA3 | Busy status output, high active

# ePaper

# Waveshare 1.54” module

Schema

Schema | ECC secure element ATECC608B-SSHDA-T

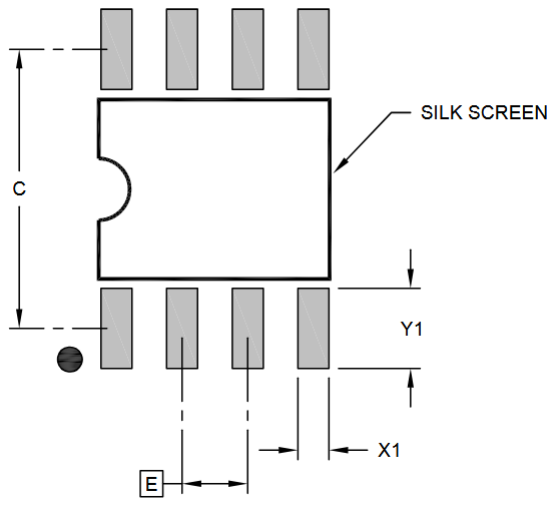
[picture p51: figure]
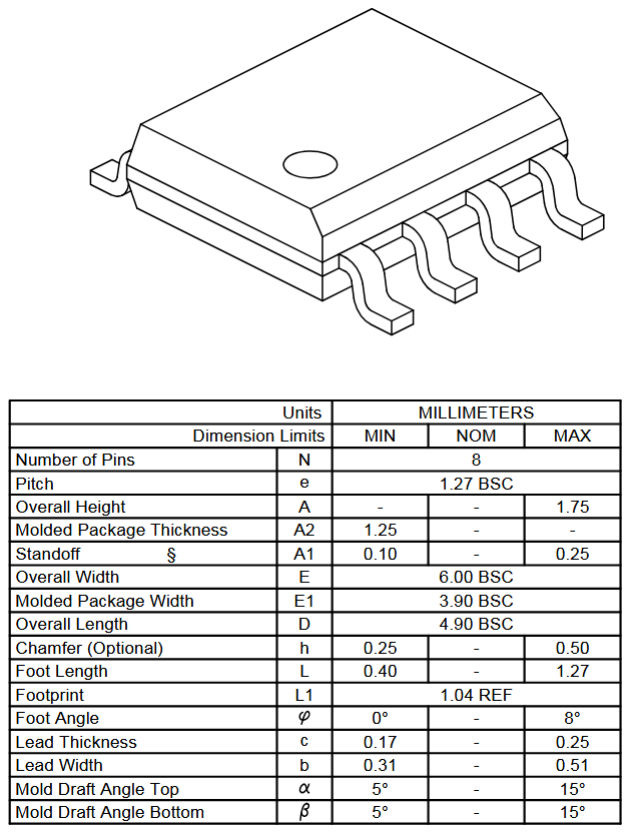
[picture p52: figure]

## Chip

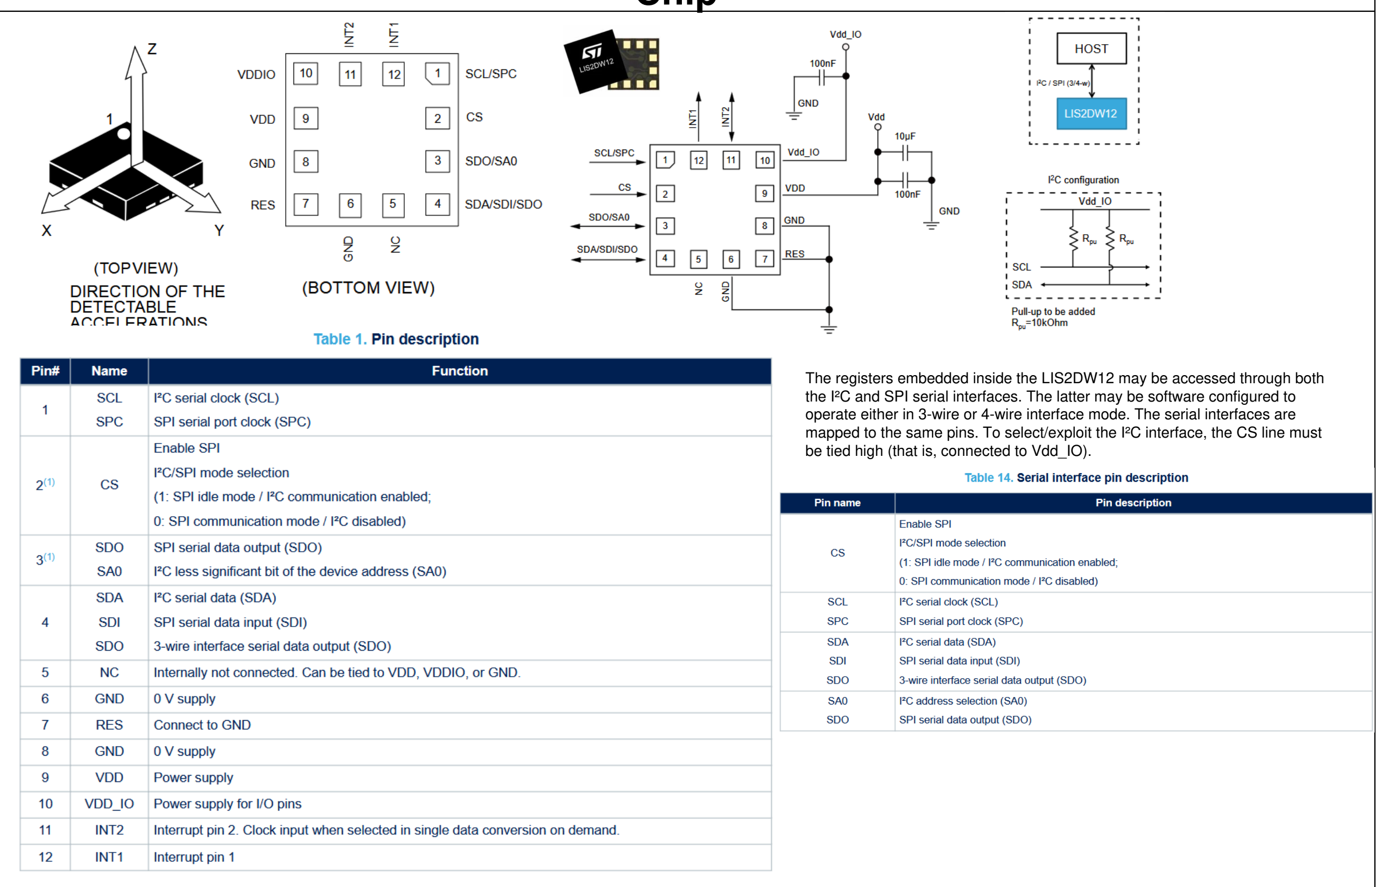
[picture p53: figure]
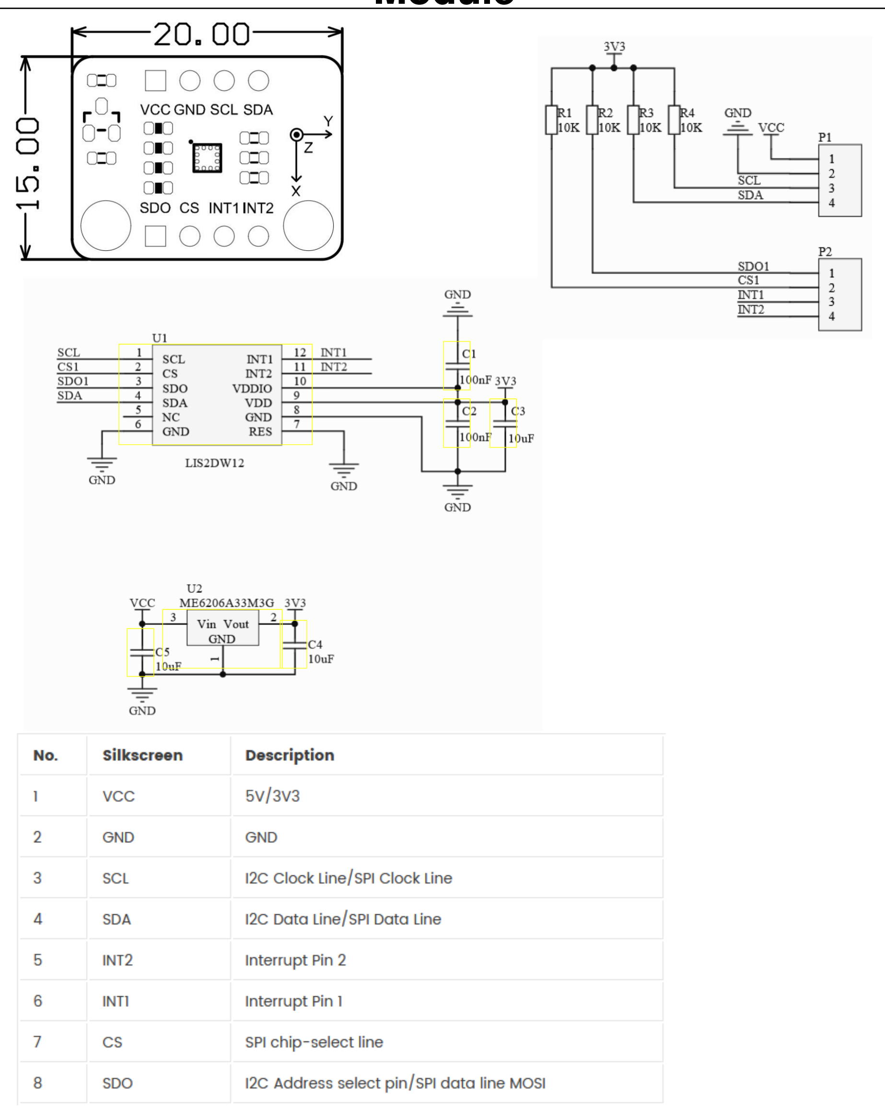
[picture p54: figure]

The registers embedded inside the LIS2DW12 may be accessed through both the I²C and SPI serial interfaces. The latter may be software configured to operate either in 3-wire or 4-wire interface mode. The serial interfaces are mapped to the same pins. To select/exploit the I²C interface, the CS line must be tied high (that is, connected to Vdd_IO).

## Module

# Schema Accelerometer LIS2DW12

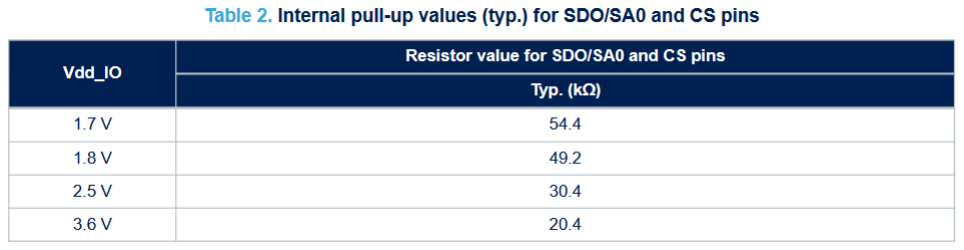
[picture p55: figure]

# FRAM

# FM24V01A-GTR

## Schema

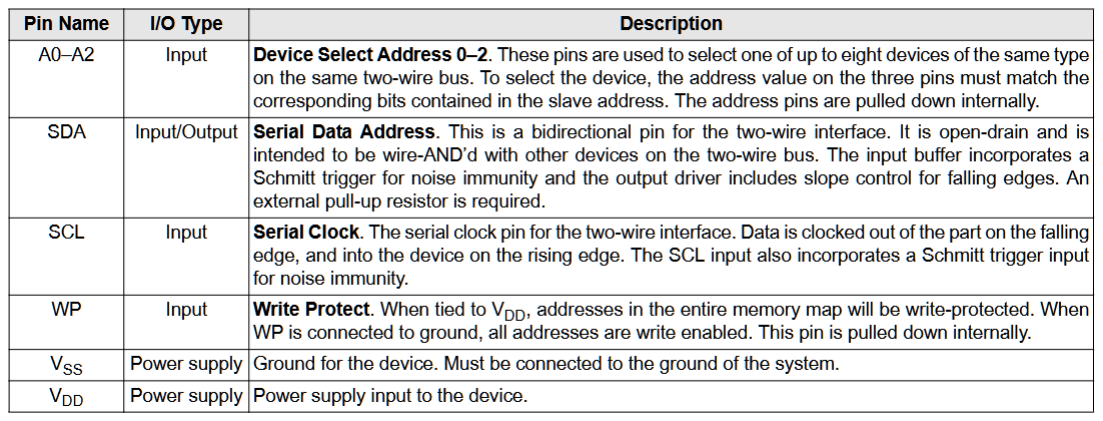
[picture p56: figure]
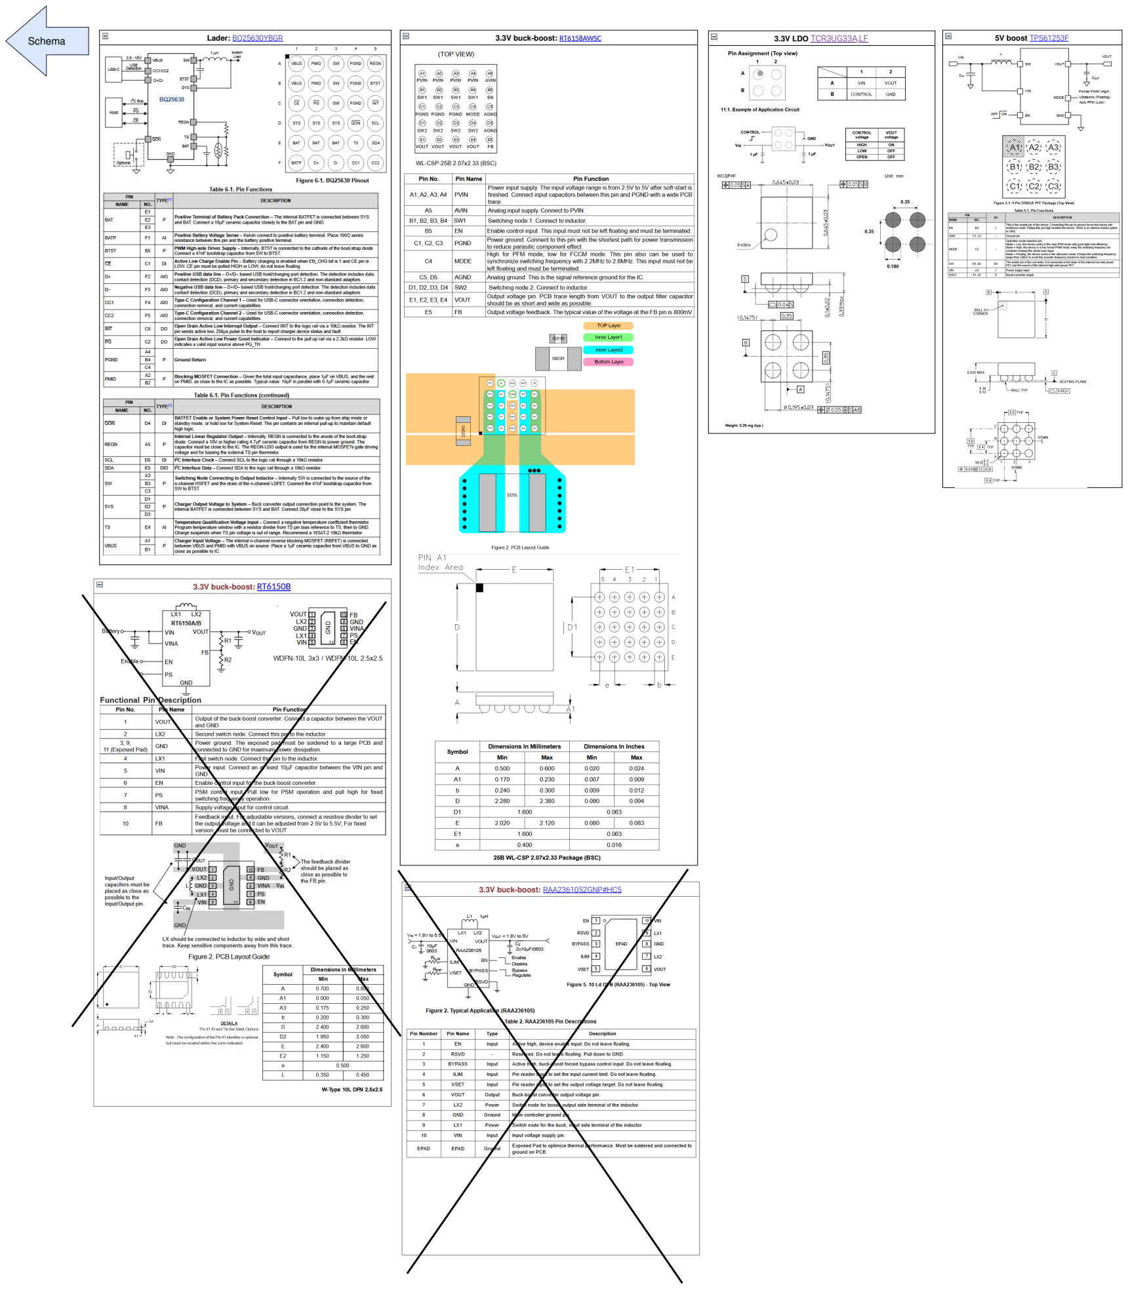
[picture p57: page 9]

Lader: BQ25630YBGR

3.3V buck-boost: RAA2361052GNP#HC5

3.3V LDO TCR3UG33A,LF | 5V boost TPS61253F

3.3V buck-boost: RT6150B

3.3V buck-boost: RT6158AWSC Schema

# Command signal: Pulse width modification High = 3 - 5V -> no level shifter needed

Schema Servo motor TD-8120MG (https://www.tinytronics.nl/en/mechanics-and-actuators/motors/servomotors/td-8120mg-waterproof-digital-servo-20kg)

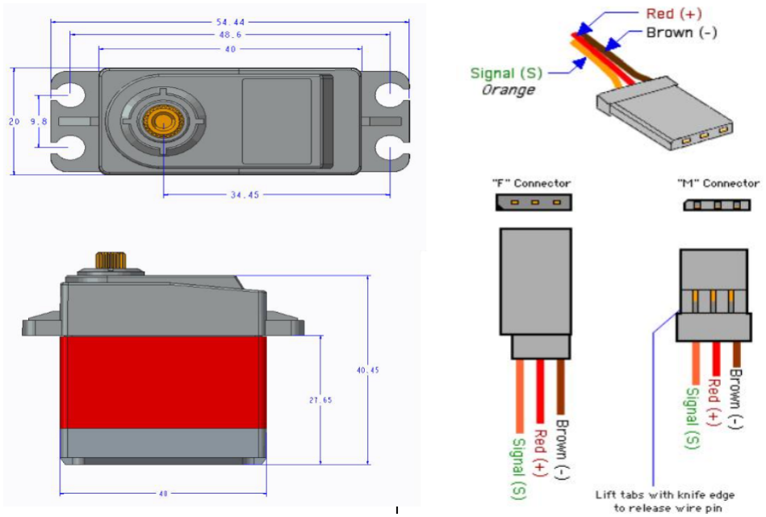
[picture p58: figure]

Schema Hall sensors (2) DRV5032DULPGM (https://www.mouser.be/ProductDetail/Texas-Instruments/DRV5032DULPGM?qs=OlC7AqGiEDk9MwfBkgsRPw%3D%3D)

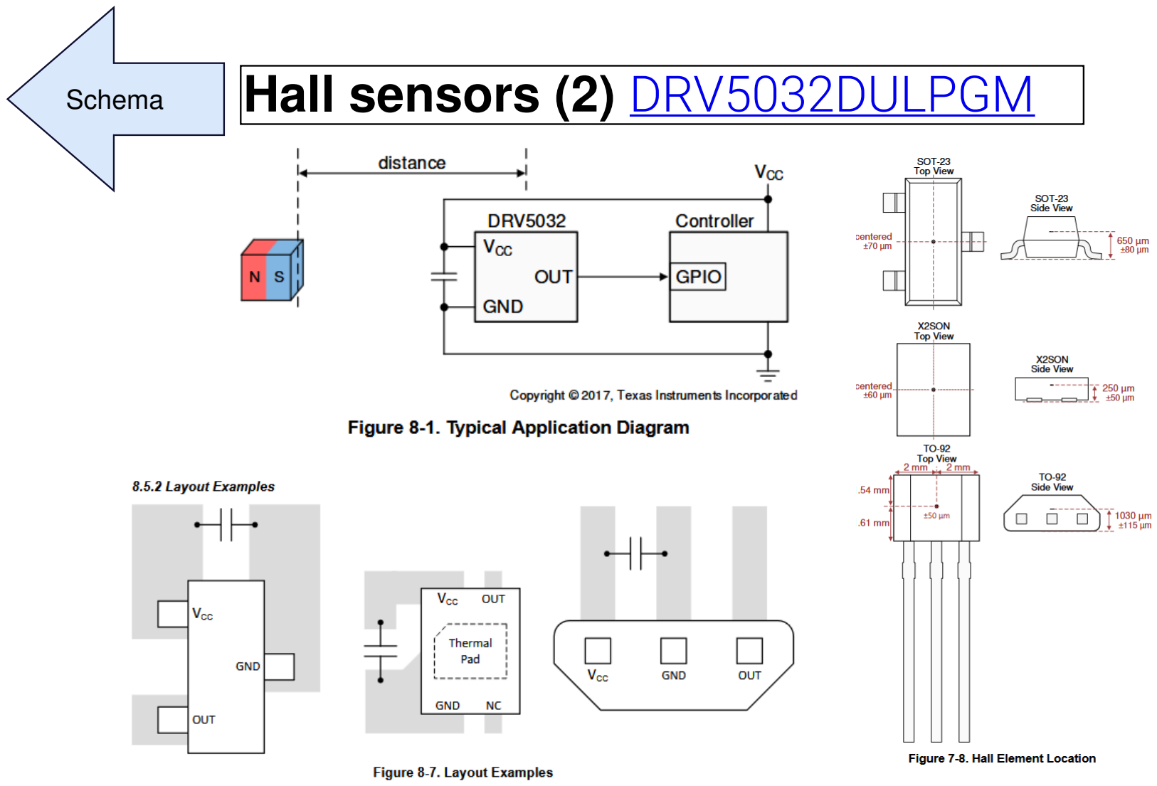
[picture p59: page 11]

Schema | LED: BL-BEG204-7-E (https://www.digikey.be/nl/products/detail/american-bright-optoelectronics-corporation/BL-BEG204-7-E/22486902)

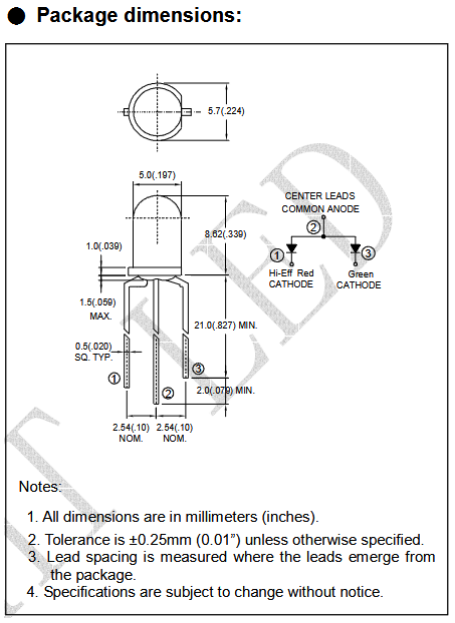
[picture p60: figure]

Schema STLINK-V3MINIE (https://www.st.com/en/development-tools/stlink-v3minie.html?ecmp=tt9470_gl_link_feb2019&rt=an&id=AN6382)

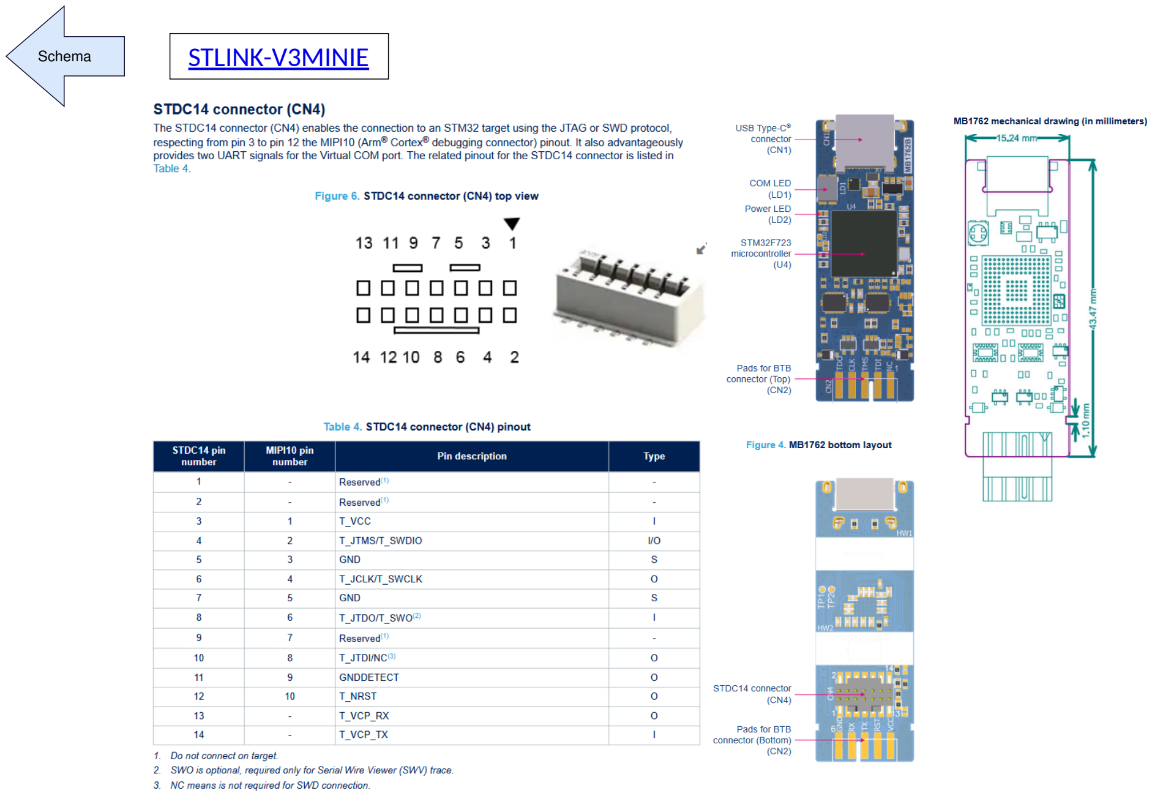
[picture p61: page 13]

Schema SD adapter module (https://www.tinytronics.nl/en/data-storage/modules/sd-card-adapter-module-3.3v-5v)

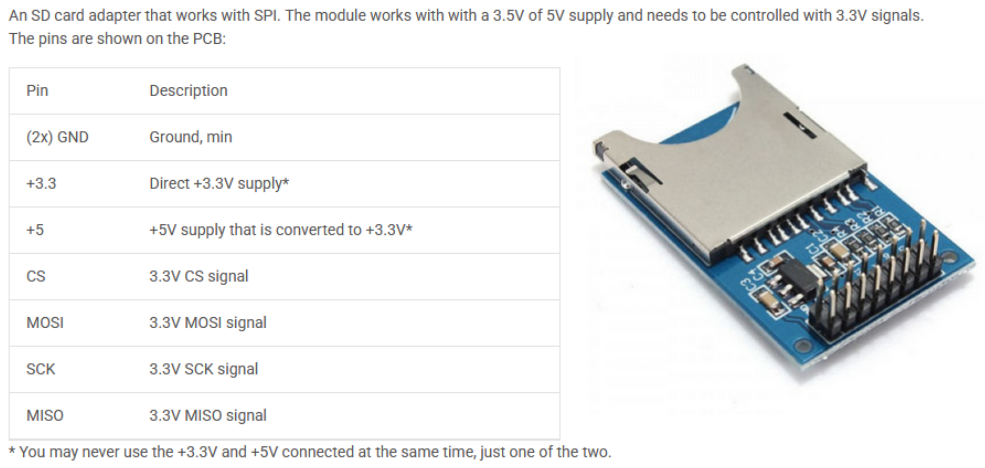
[picture p62: figure]

USB4105-GF-A-060 (https://www.mouser.be/ProductDetail/GCT/USB4105-GF-A-060?qs=QNEnbhJQKvY2mocwNJzgfA%3D%3D)

## Schema

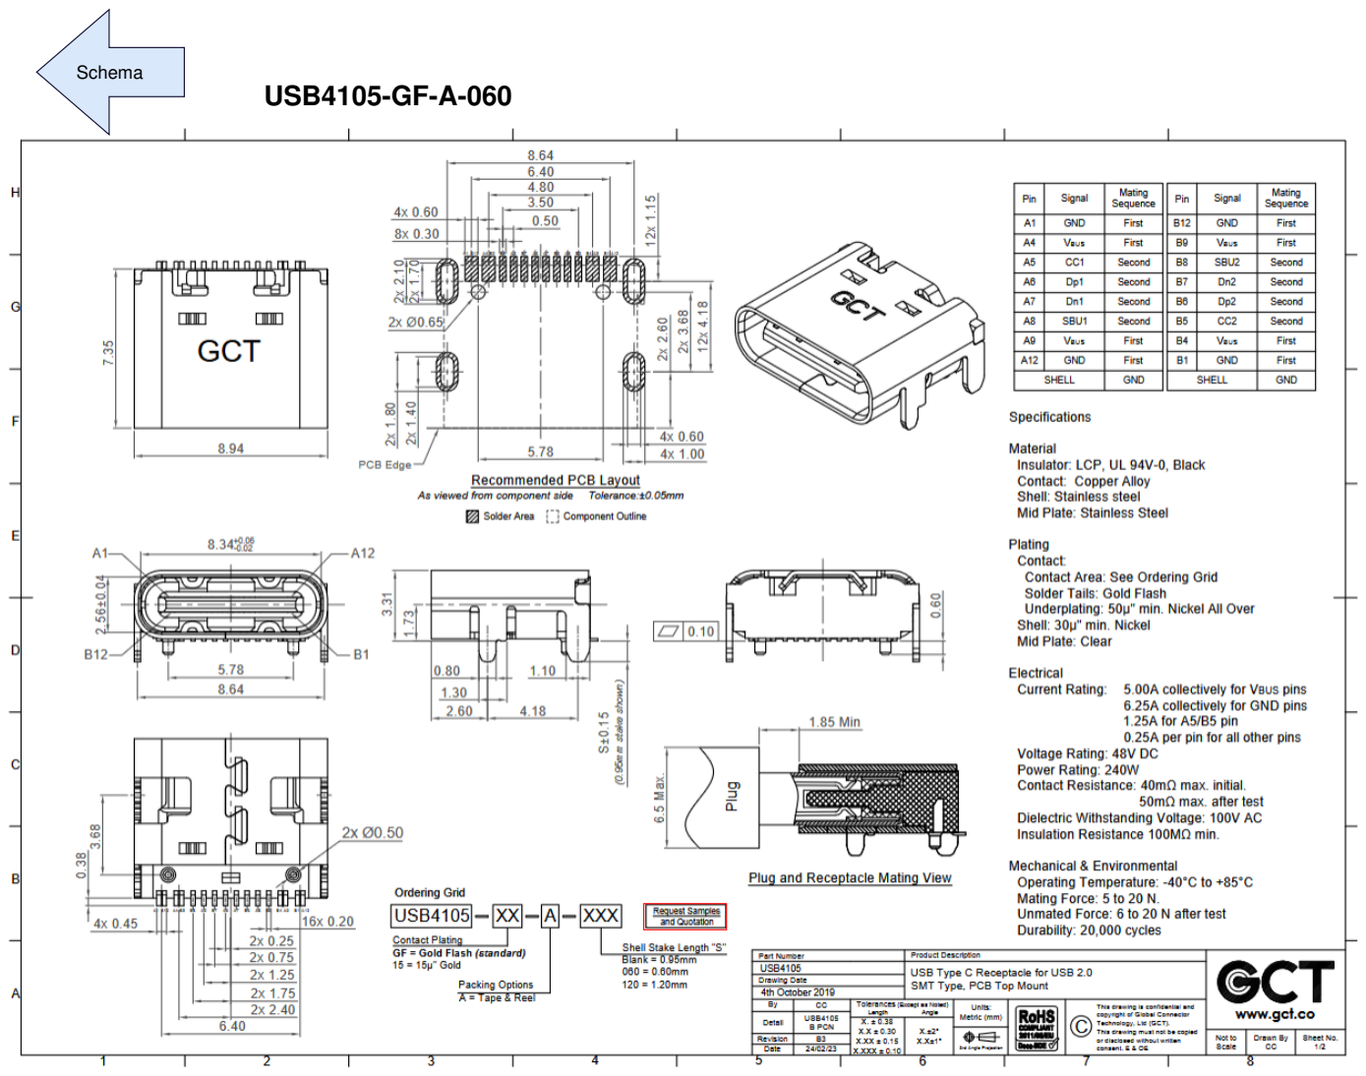
[picture p63: page 15]
