krampslaag/Bikera/Architectuurschema export png/Architectuur schema-Accelerometer.drawio.png

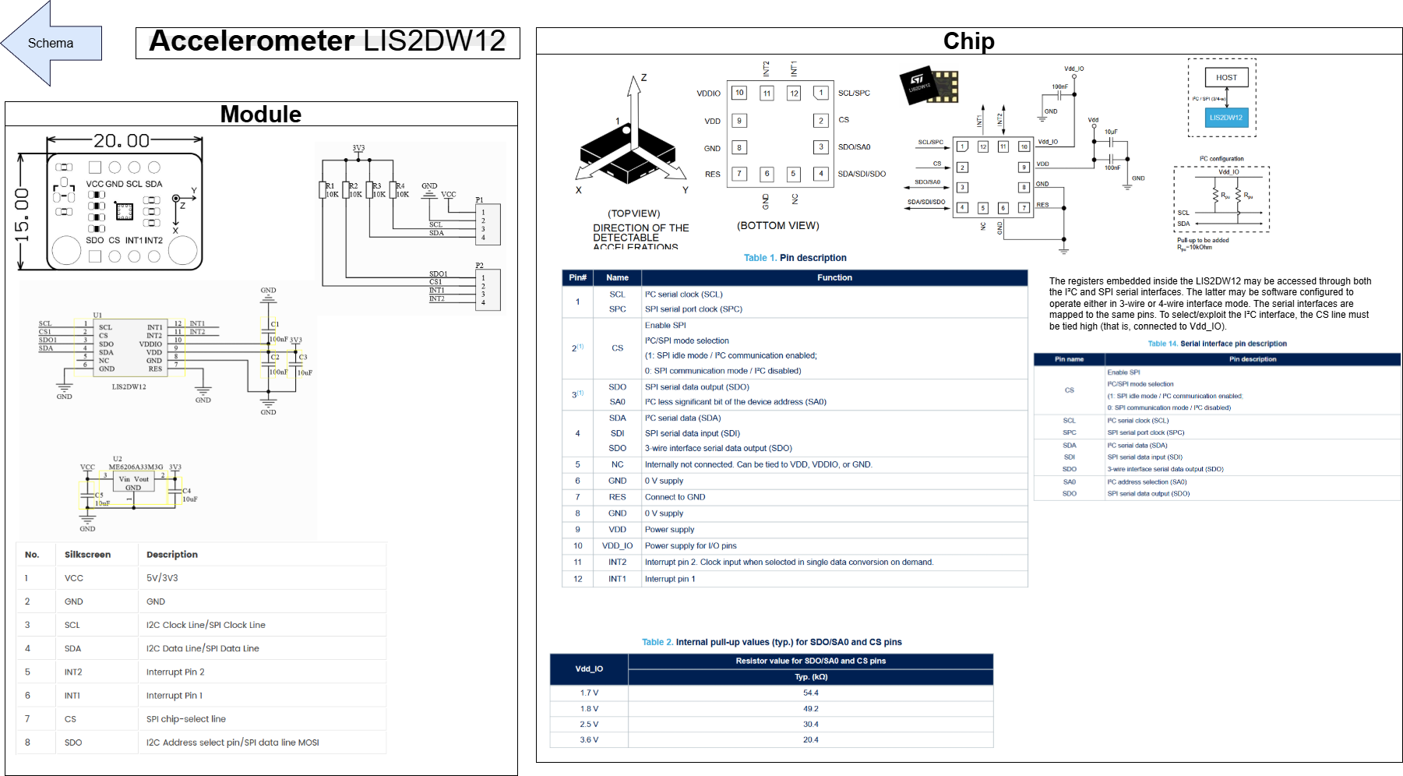
Architectuurschema export png/Architectuur schema-Accelerometer.drawio.png
