krampslaag/Bikera/Architectuurschema export png/Architectuur schema-ECC.drawio.png

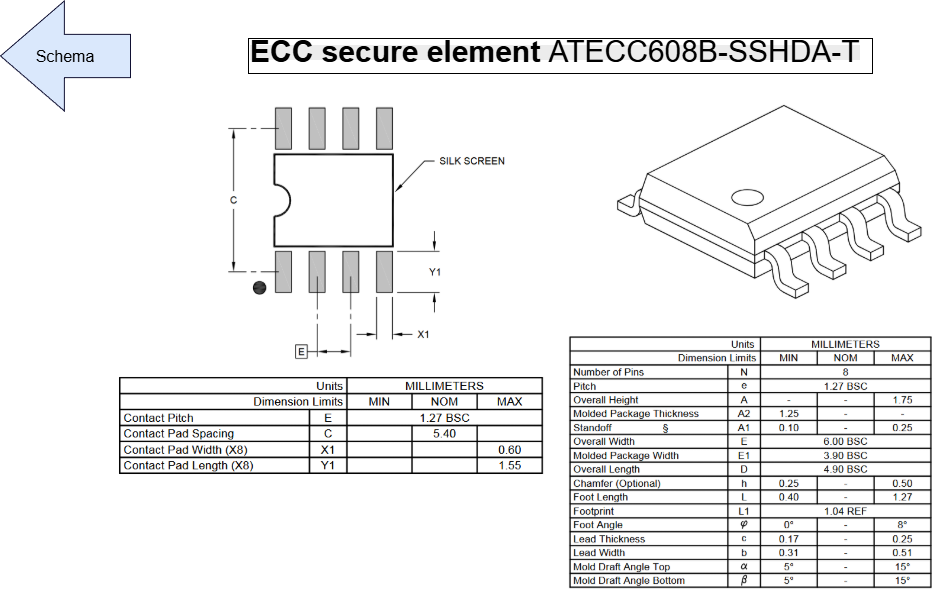
Architectuurschema export png/Architectuur schema-ECC.drawio.png
