krampslaag/Bikera/Architectuurschema export png/Architectuur schema-GPS.drawio.png

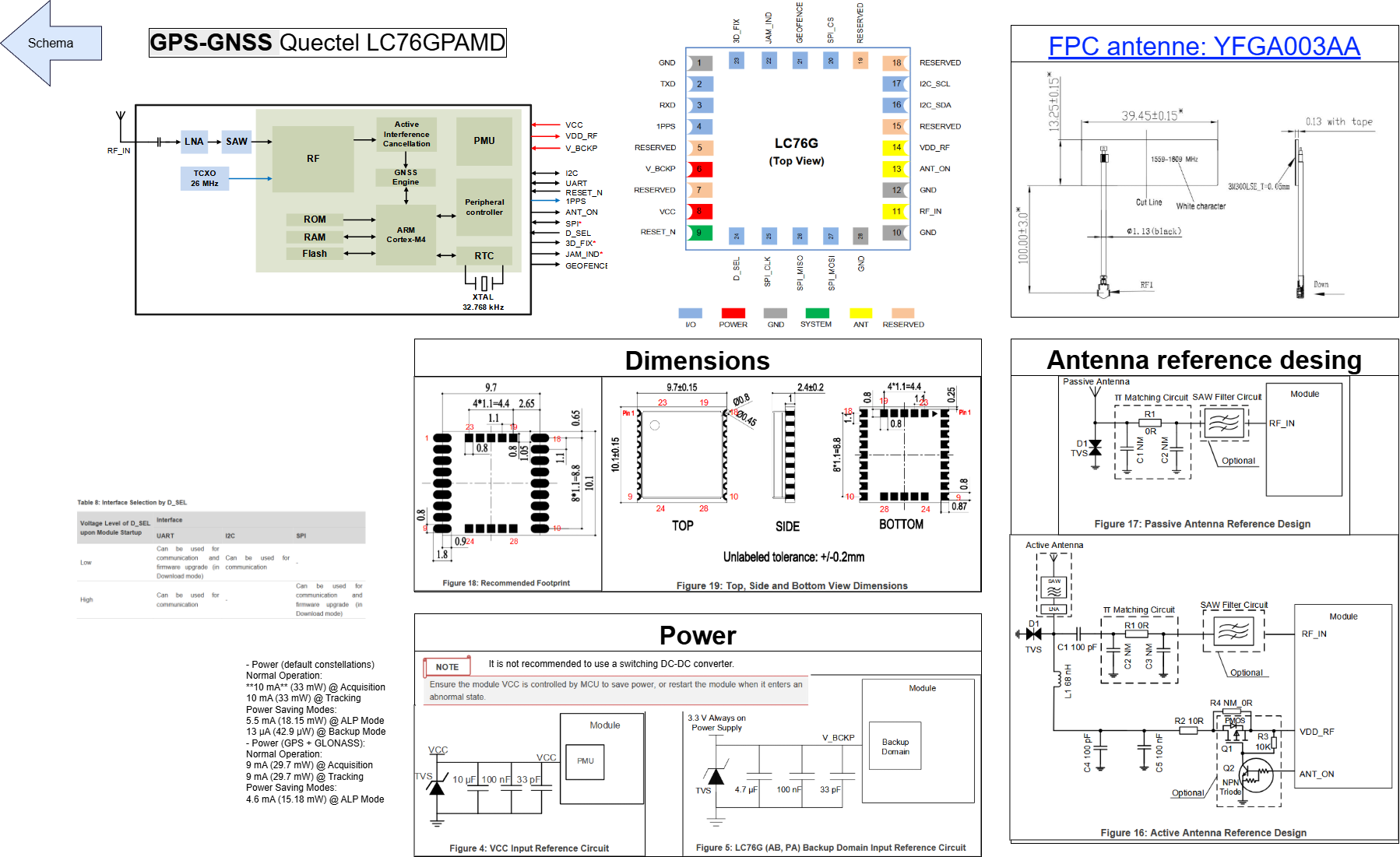
Architectuurschema export png/Architectuur schema-GPS.drawio.png
