krampslaag/Bikera/Architectuurschema export png/Architectuur schema-LED.drawio.png

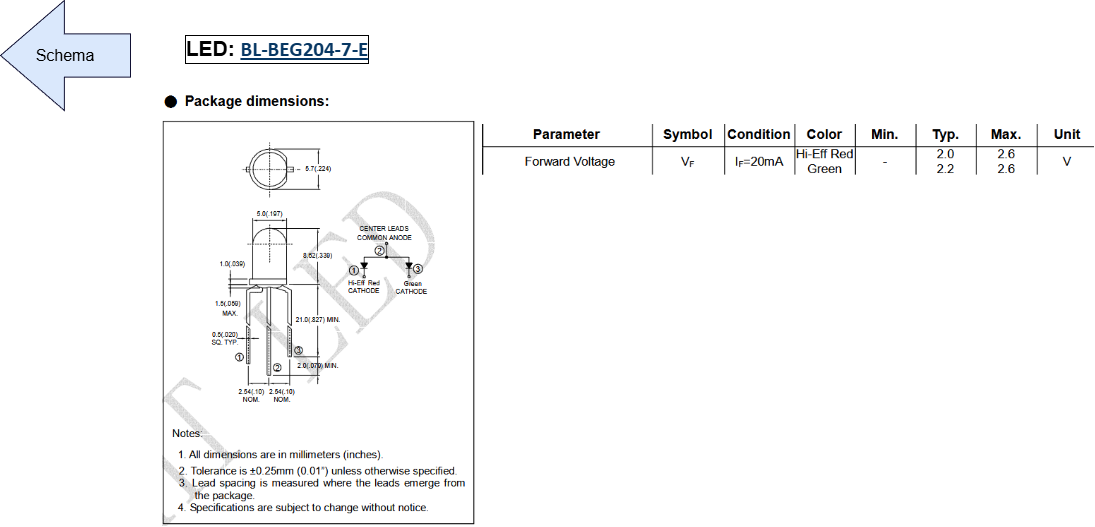
Architectuurschema export png/Architectuur schema-LED.drawio.png
