krampslaag/Bikera/Architectuurschema export png/Architectuur schema-LoRa.drawio.png

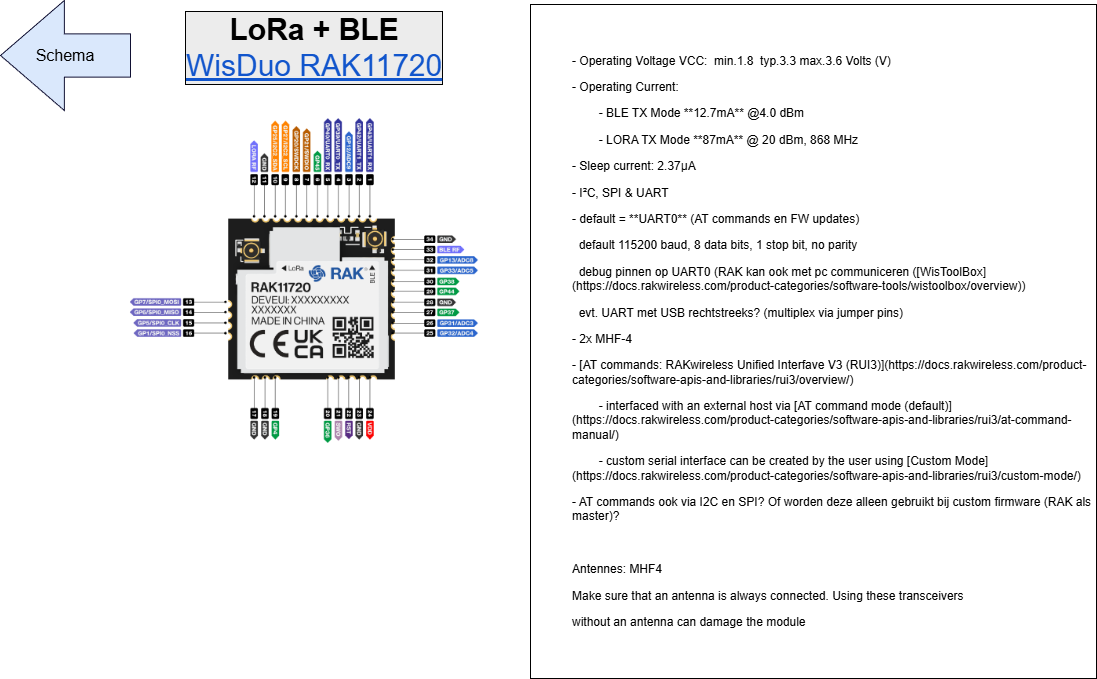
Architectuurschema export png/Architectuur schema-LoRa.drawio.png
