krampslaag/Bikera/Architectuurschema export png/Architectuur schema-Servo motor.drawio.png

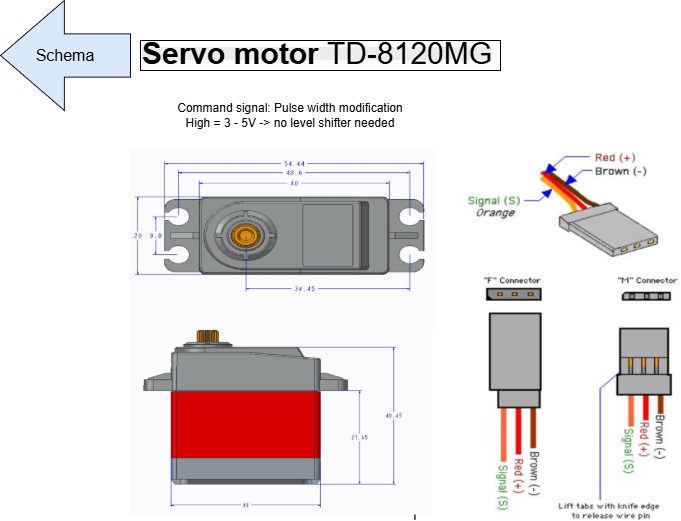
Architectuurschema export png/Architectuur schema-Servo motor.drawio.png
