krampslaag/Bikera/Architectuurschema export png/Architectuur schema-STM32.drawio.png

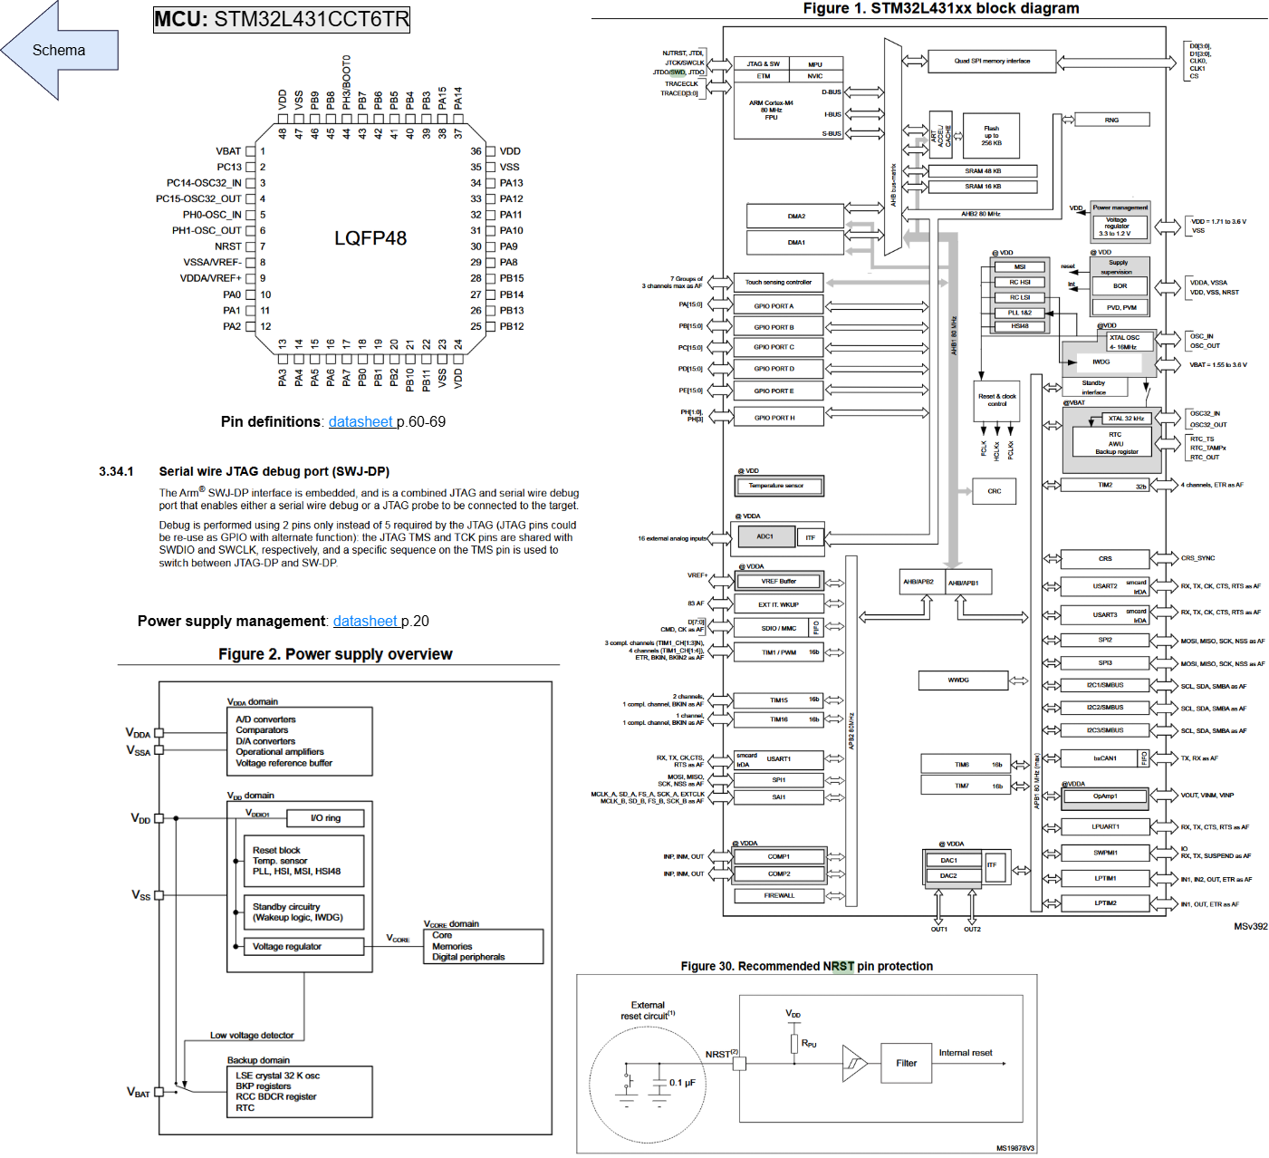
Architectuurschema export png/Architectuur schema-STM32.drawio.png
