krampslaag/Bikera/Kicad_v2/layout_top_plan.png

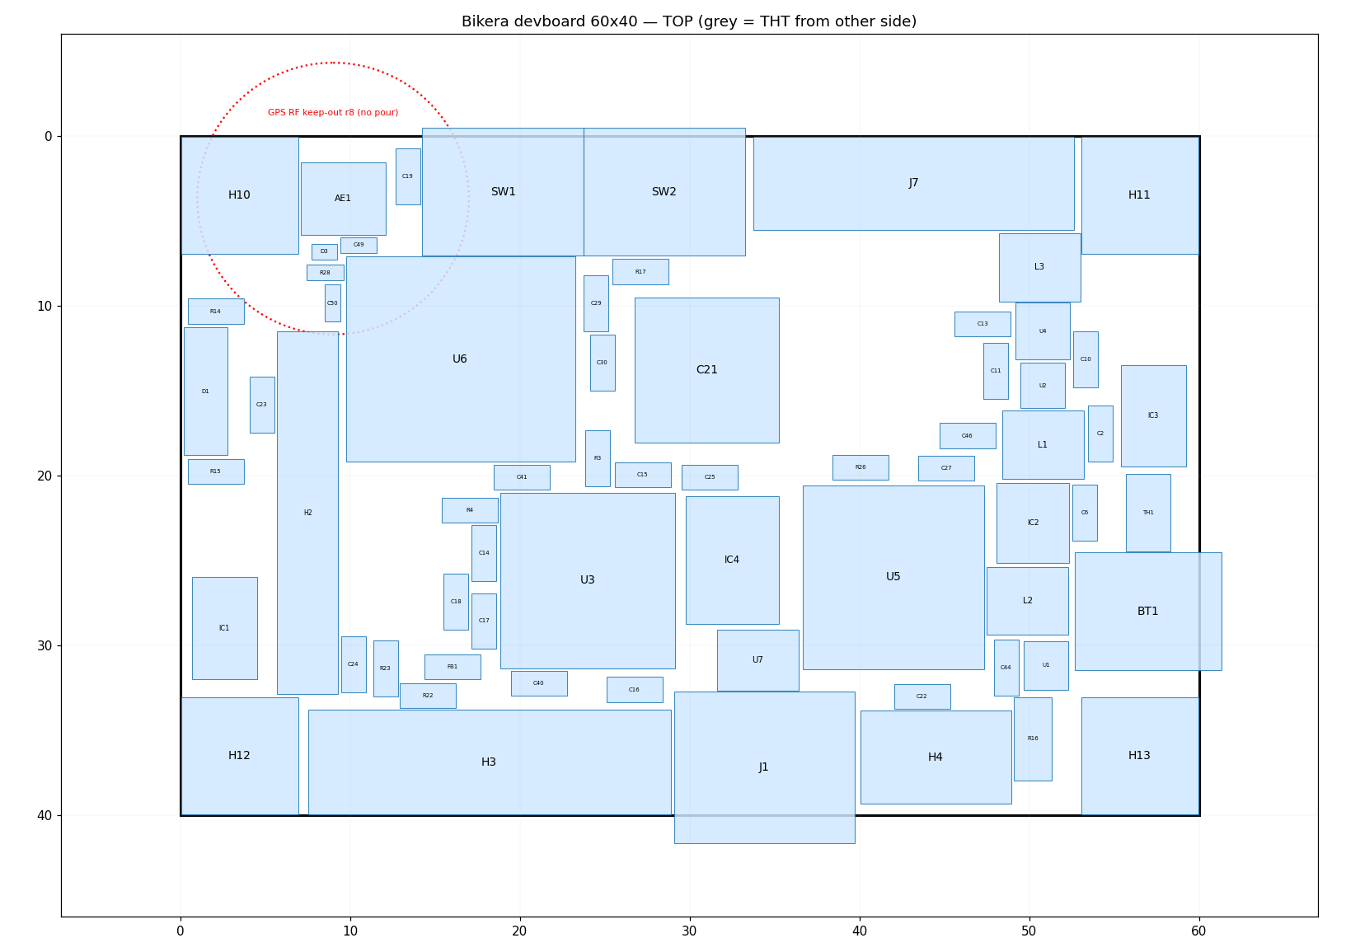
Kicad_v2/layout_top_plan.png
