krampslaag/Bikera/Kicad_v2/routed_bottom.png

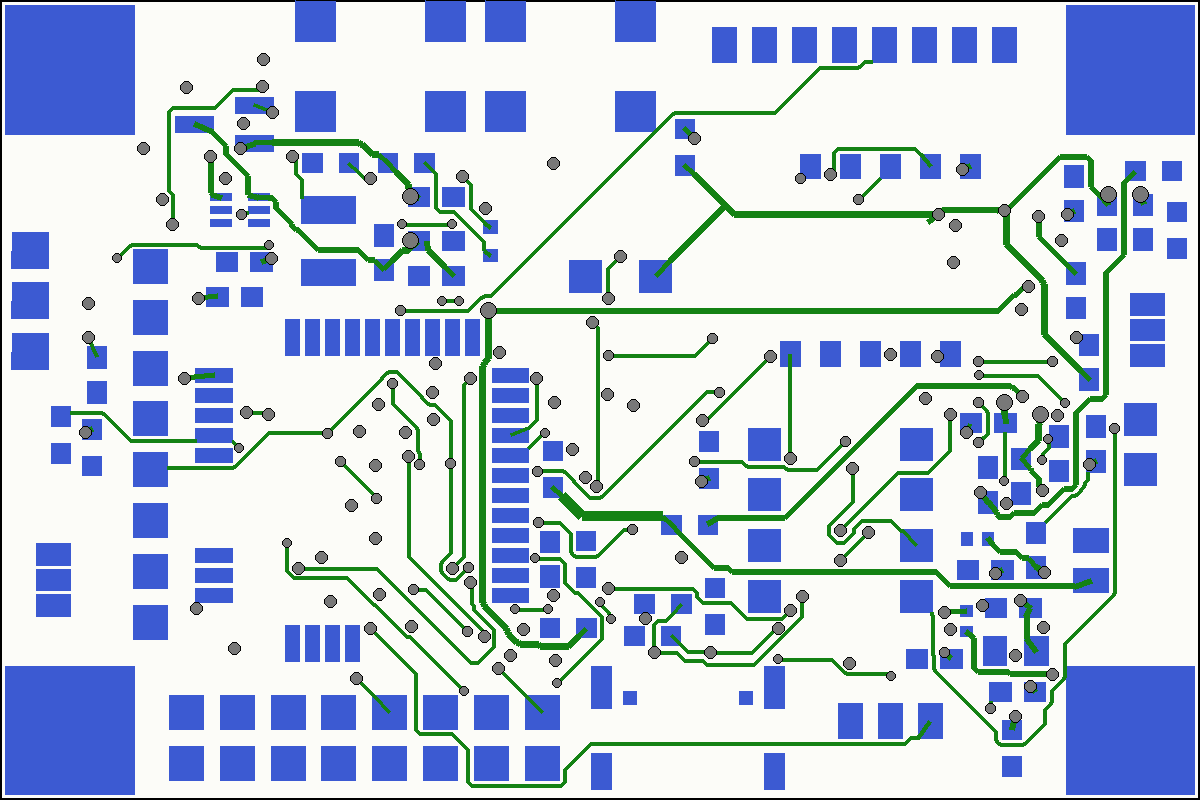
Kicad_v2/routed_bottom.png
