krampslaag/Bikera/Kicad_v2/routed_top.png

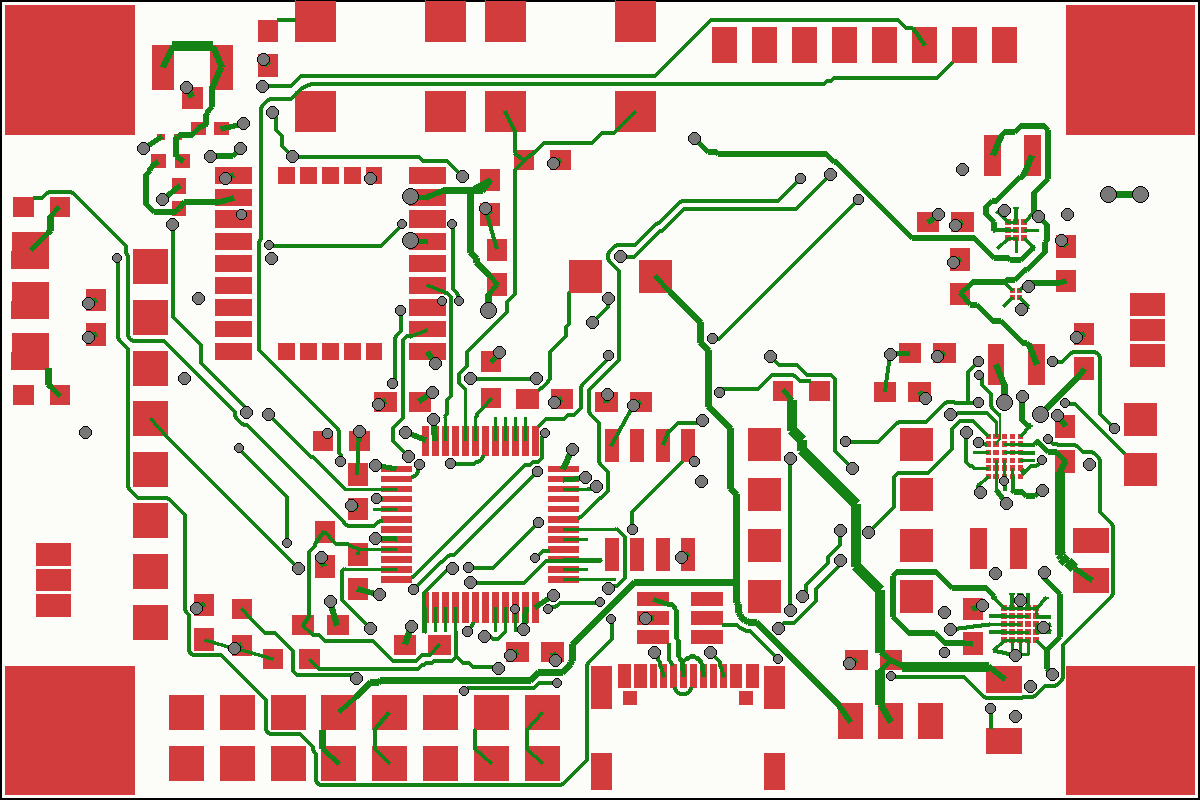
Kicad_v2/routed_top.png
