krampslaag/Bikera/Kicad_v2/layout_pads_verification.png

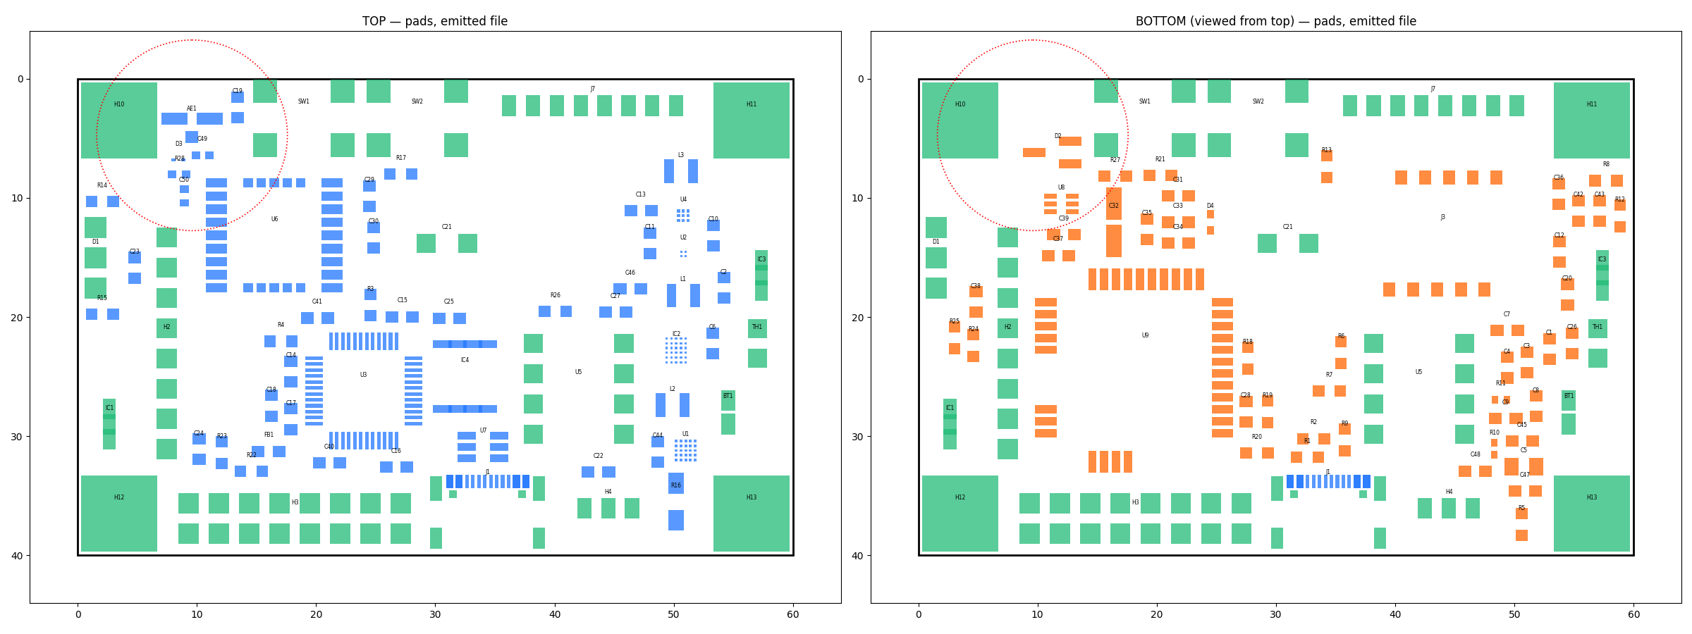
Kicad_v2/layout_pads_verification.png
